Archive-663/kodakFunsaver/Canon FD/README.md

## Kodak Funsaver lens rehousing for Canon FD

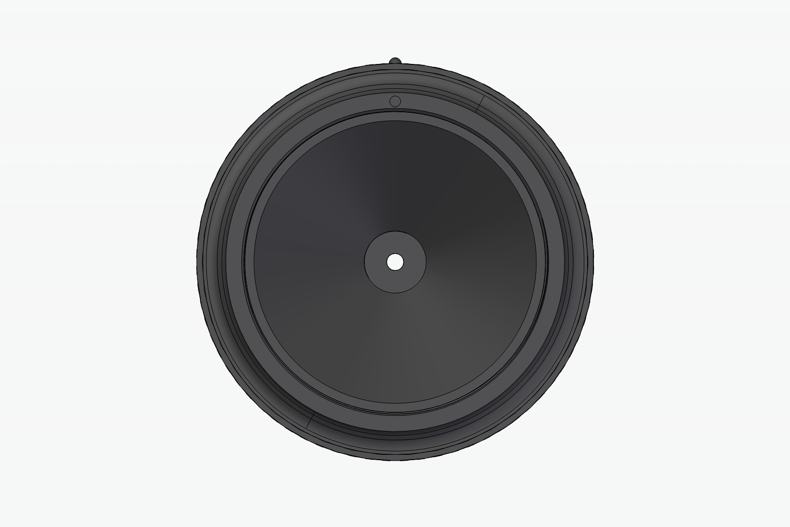
[picture p43: ASSETS/kodakFunsaver_canonFD.jpg]
KFS_canonFD_1

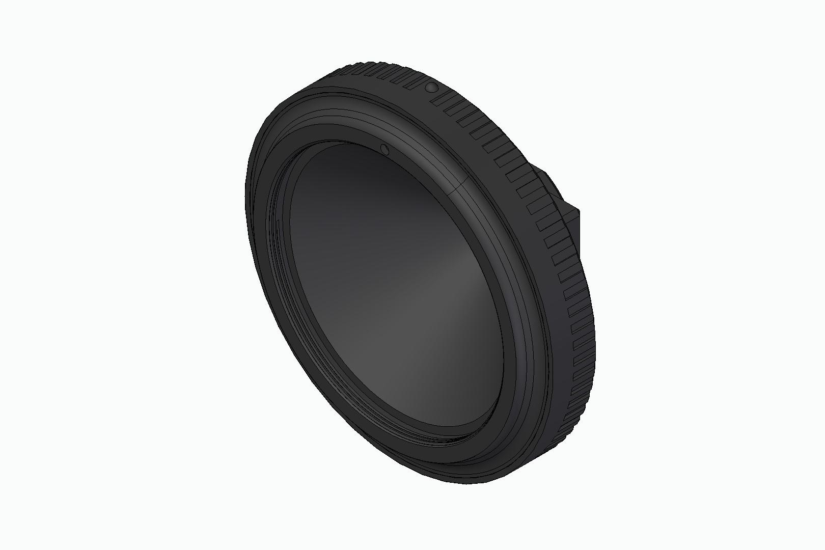
[picture p44: ASSETS/kodakFunsaver_canonFD_1.jpg]
KFS_canonFD_2

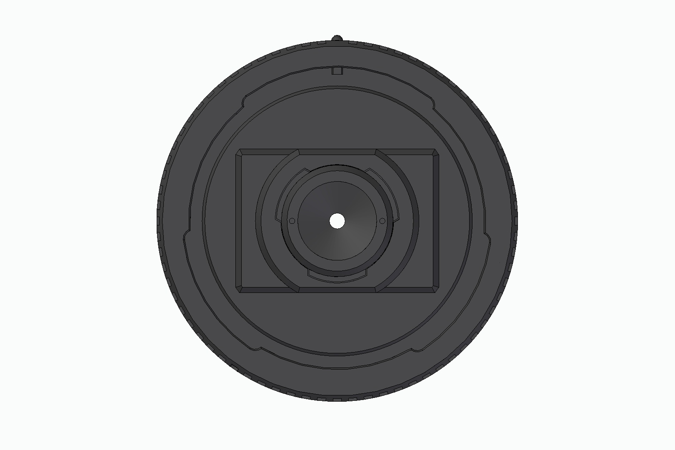
[picture p45: ASSETS/kodakFunsaver_canonFD_2.jpg]
KFS_canonFD_3


### Features:
- Breech-lock mounting ring for DSLR/SLR cameras
- Standard mounting for Mirrorless cameras
- 30mm focal length
- Fixed ~f11 aperture
- Available in: Canon EF, EF-S, FD, RF; Fuji X; Leica M; M42; Nikon F DX, F FX, Z; Sony E

### Compatibility Note:
You need a Canon body that allows for mirror lock up. Some older film cameras allowed you to hold the mirror up with hardware, but there are some that link the mirror actuation to the shutter actuation so you can't lock your mirror up. Just make sure you have mirror lock up. Tested on a Canon FTb.

### What you’ll need:
- A few of M1.6 x 5mm machine screws (PETG)
  or
- A few of M1.6 x 5mm self tapping screws (PETG or ABS)
- Lens from a Kodak FunSaver (2015 and newer)
- Viewfinder lenses from a Kodak FunSaver (2015 or newer) for
  
  [Kodak Funsaver Viewfinder Housing](https://github.com/Archive-663/kodakFunsaver/tree/main/viewFinder)
  
- [49mm Lens Cap](https://github.com/Archive-663/lensCaps)

### What would be helpful:
- M1.4 drill bit
- M1.8/M2 drill bit
- digi-Process C-41 Lightroom Preset

    [Lightroom Presets](https://github.com/Archive-663/lightroomPresets)

    This preset develops your photos for a flat base reminiscent of old Kodak negative scans. It does not remove the distortion as it is a characteristic of the lens and of the photos that are produced with film. If you want to remove the distortion; set your distortion slider to ~ -12.

### Helpful Links:
- [Kodak FunSaver Disassembly](https://www.youtube.com/watch?v=eMyq5sUIDkU)

- [Kodak FunSaver Lens Removal](https://www.youtube.com/watch?v=mniP1P2PrpM)

- [Kodak FunSaver Lens Adapter Assembly](https://www.youtube.com/watch?v=7Ed5-oDCAb8)

### Printing help:
I print with PETG because it's pretty easy to set up with and dial in. If you want to use something else, go for it. I'd stay away from PLA because it's not the best in heat and against solvents. 

Generally, all my designs have chamfers on the print face of the STL.

Please view the printOrientation.3mf file for help with orienting the parts on the printer bed. 

### Assembly help:
I suggest drilling holds to their correct tap size before tapping. The m1.6 holes should be drilled out to 1.4 then tapped with the m1.6 tap. The Rotator holes should be drilled out with an m2 or m1.8 drill bit.

When assembling the rotating assemblies use some synthetic grease similar to Super Lube PTFE or keycap lube to make the rotate function smoother. 

Please view the _assembly.stp file for help in parts orientation. If you do not have a CAD program, <a href="https://www.freecad.org/downloads.php" target="_blank">download FreeCAD</a> to view the assembly file and better understand how it should assemble.

### Help support Archive 663 with a dontation or monthly sub
