Archive-663/kodakFunsaver/ASSETS/kodakFunsaver_sample (1).jpg

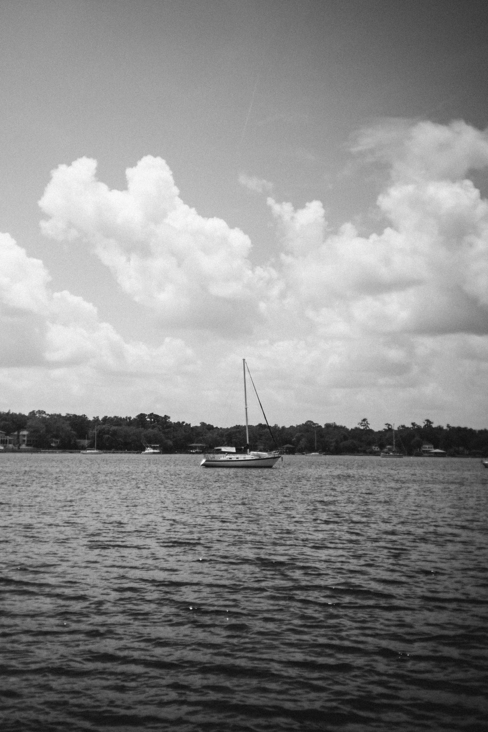
ASSETS/kodakFunsaver_sample (1).jpg
