Archive-663/kodakFunsaver/ASSETS/kodakFunsaver_sample (2).jpg

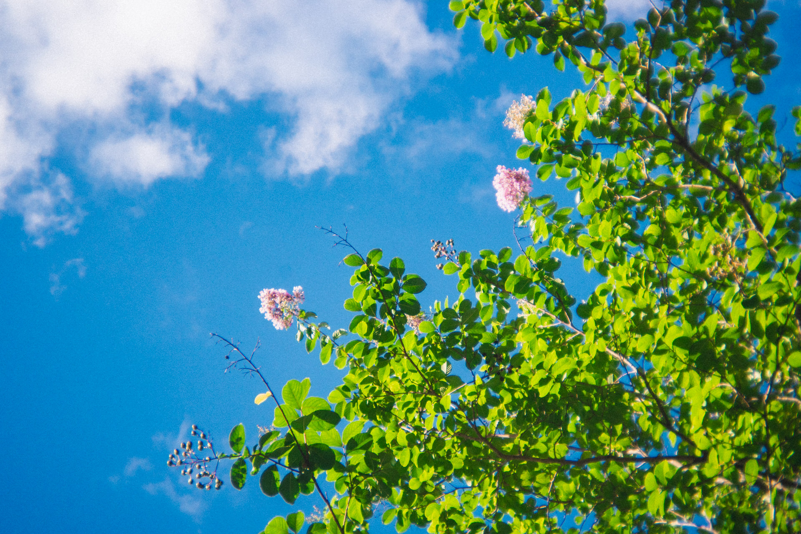
ASSETS/kodakFunsaver_sample (2).jpg
