Archive-663/kodakFunsaver/ASSETS/kodakFunsaver_sample (3).jpg

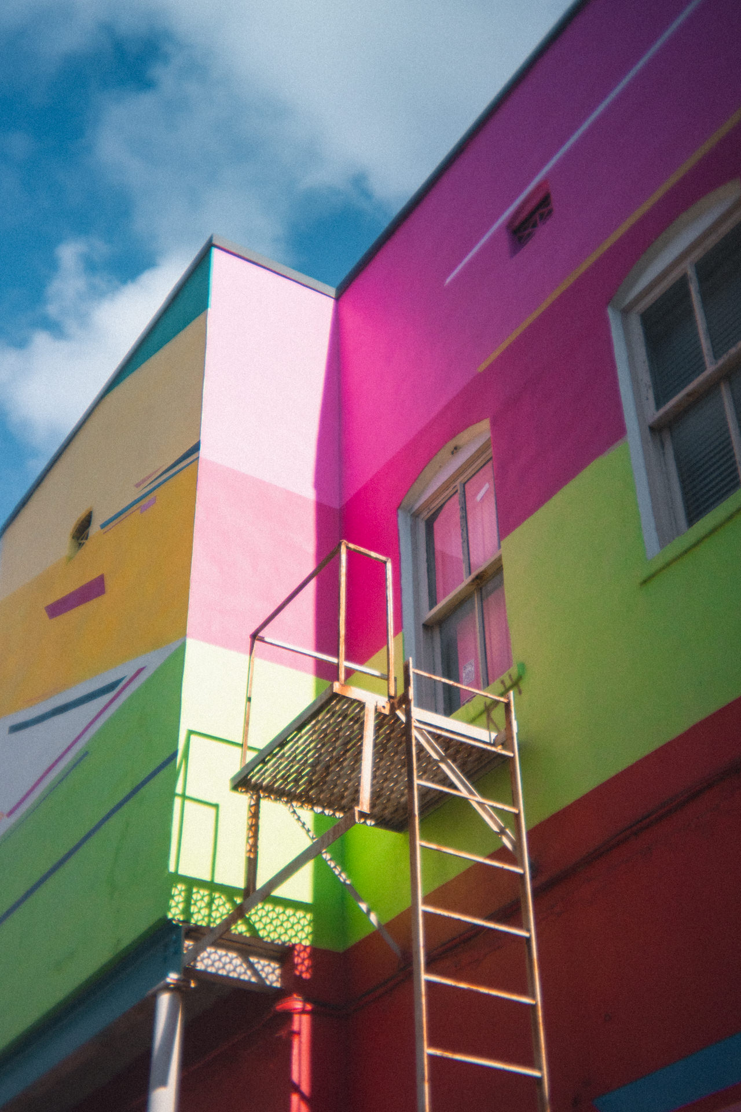
ASSETS/kodakFunsaver_sample (3).jpg
