Archive-663/kodakFunsaver/ASSETS/kodakFunsaver_sample (4).jpg

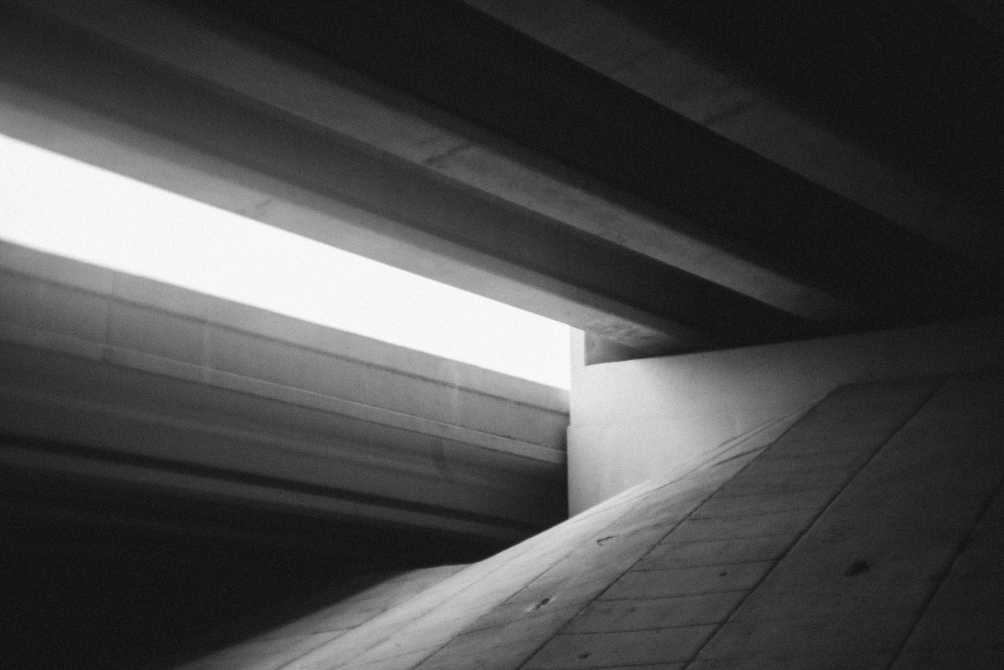
ASSETS/kodakFunsaver_sample (4).jpg
