Archive-663/kodakFunsaver/ASSETS/kodakFunsaver_sample (7).jpg

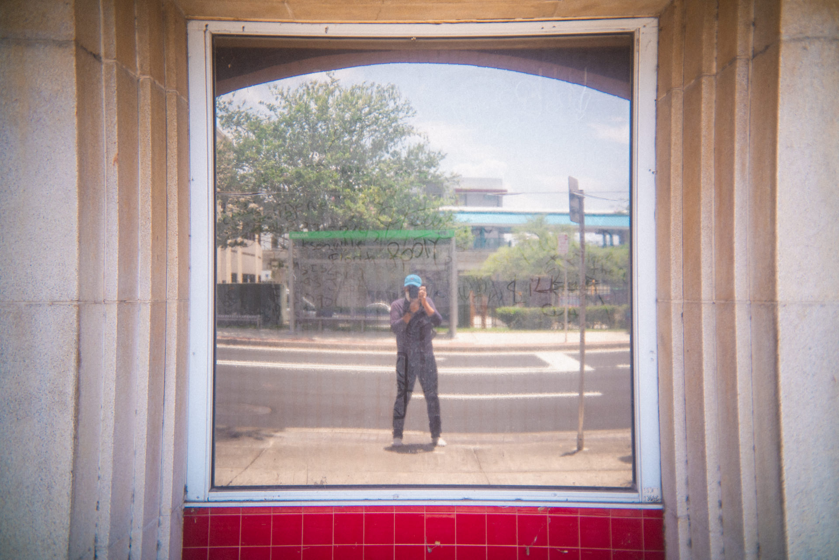
ASSETS/kodakFunsaver_sample (7).jpg
