Archive-663/kodakFunsaver/ASSETS/kodakFunsaver_sample (8).jpg

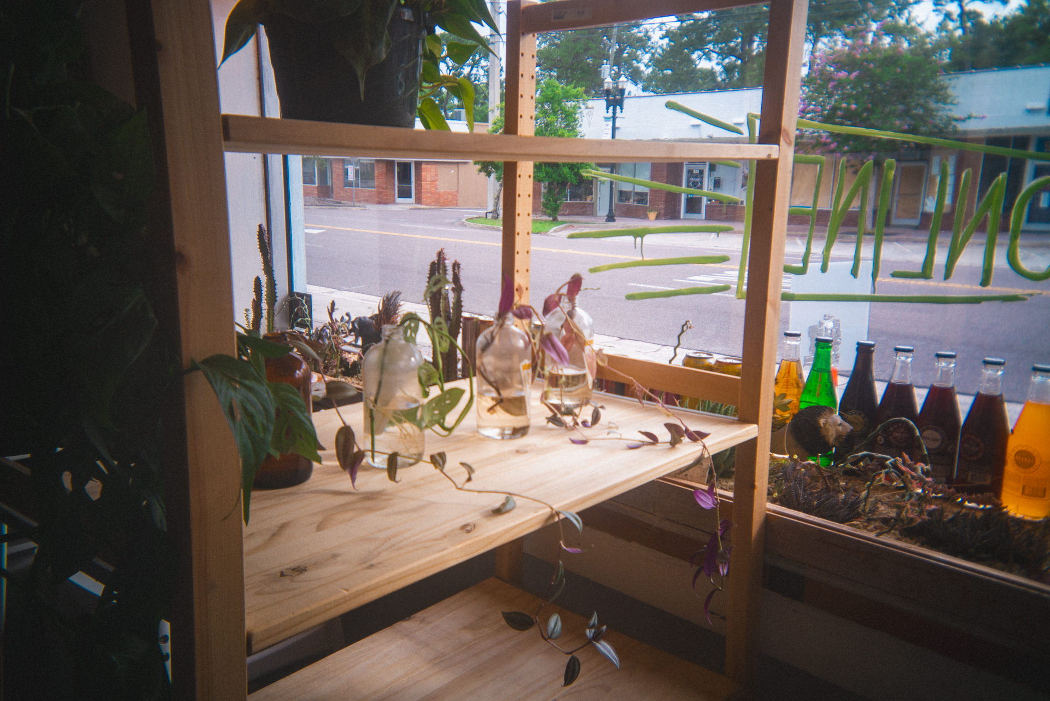
ASSETS/kodakFunsaver_sample (8).jpg
