Archive-663/kodakFunsaver/ASSETS/kodakFunsaver_sample (9).jpg

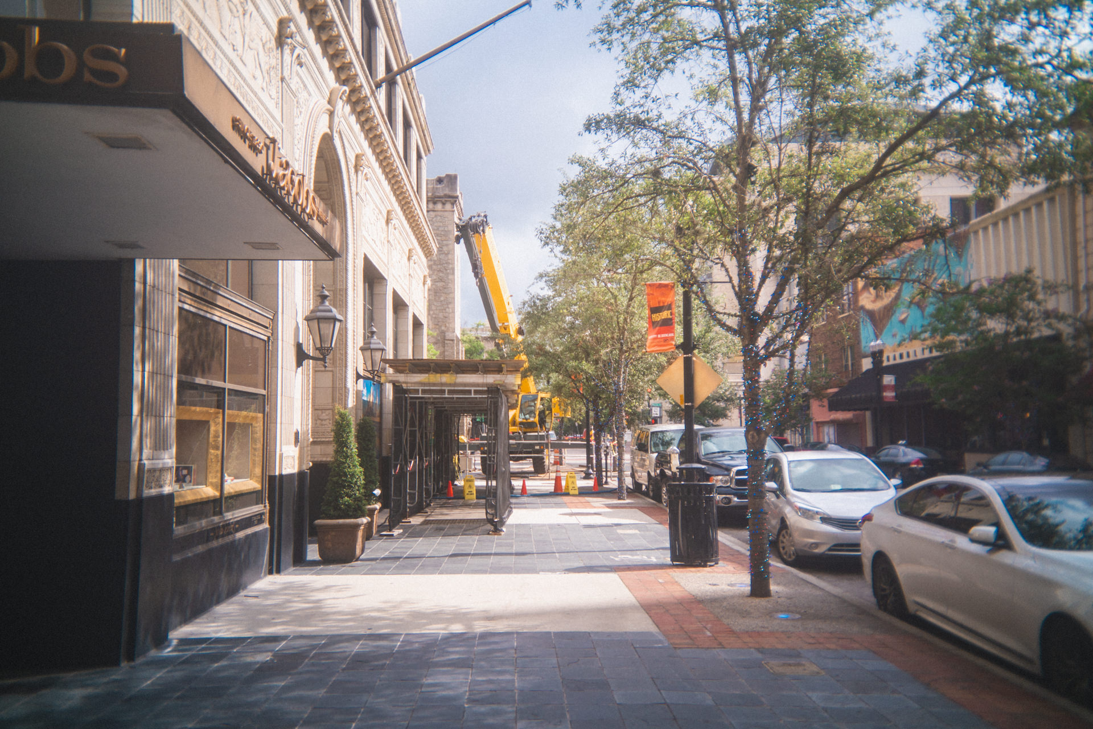
ASSETS/kodakFunsaver_sample (9).jpg
