Archive-663/kodakFunsaver/ASSETS/kodakFunsaver_sample (10).jpg

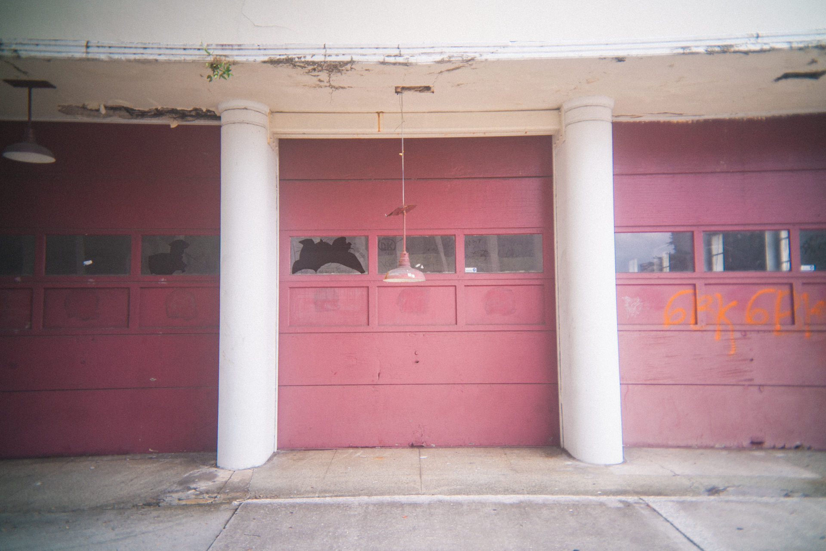
ASSETS/kodakFunsaver_sample (10).jpg
