Archive-663/kodakFunsaver/ASSETS/kodakFunsaver_sample (11).jpg

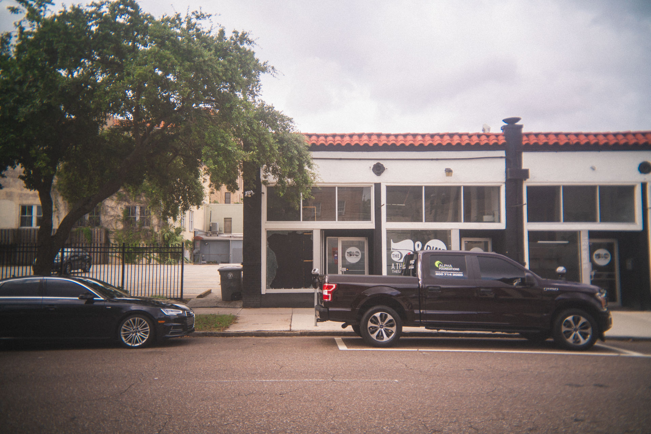
ASSETS/kodakFunsaver_sample (11).jpg
