Archive-663/kodakFunsaver/ASSETS/kodakFunsaver_sample (12).jpg

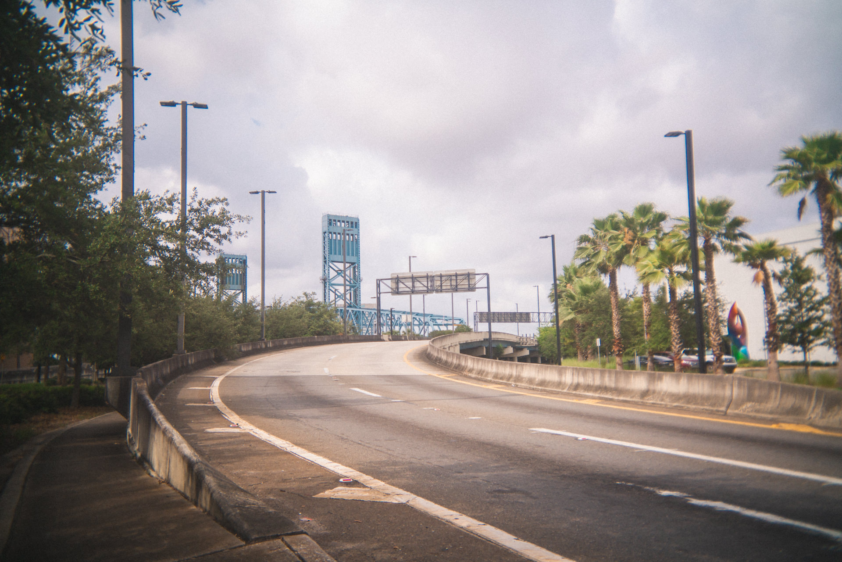
ASSETS/kodakFunsaver_sample (12).jpg
