Archive-663/kodakFunsaver/ASSETS/kodakFunsaver_sample (13).jpg

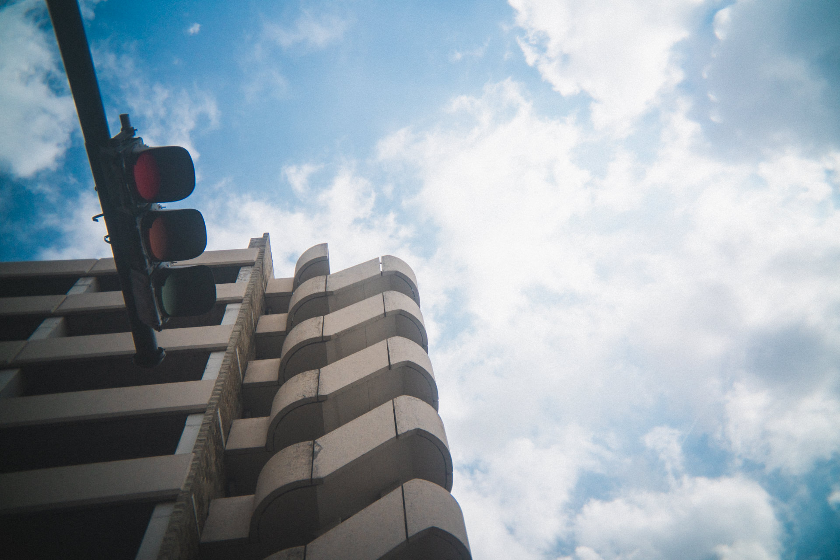
ASSETS/kodakFunsaver_sample (13).jpg
