Archive-663/kodakFunsaver/ASSETS/kodakFunsaver_sample (14).jpg

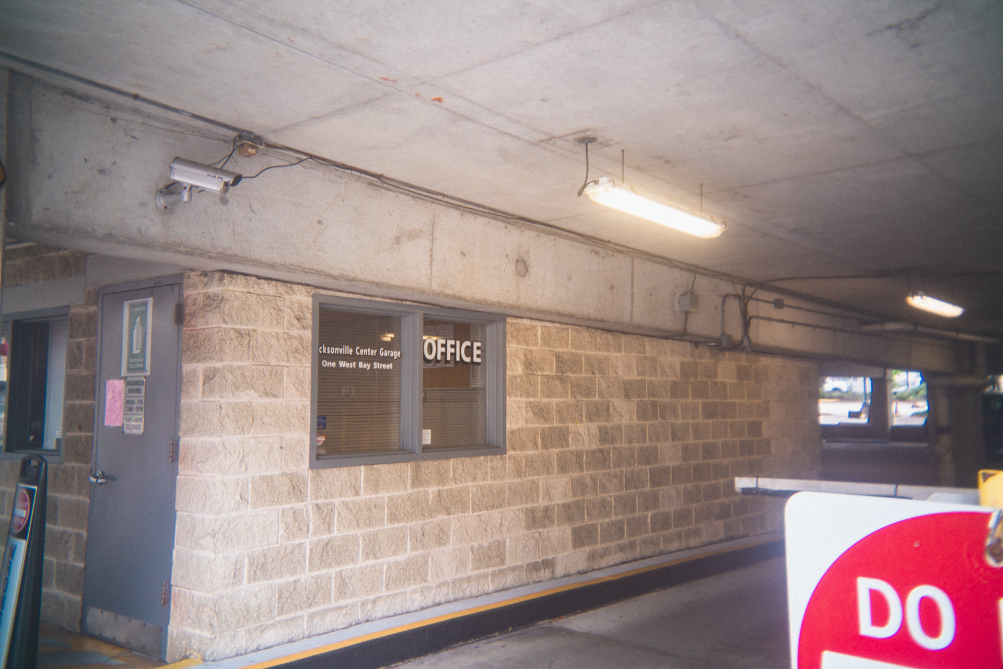
ASSETS/kodakFunsaver_sample (14).jpg
