Archive-663/kodakFunsaver/ASSETS/kodakFunsaver_sample (15).jpg

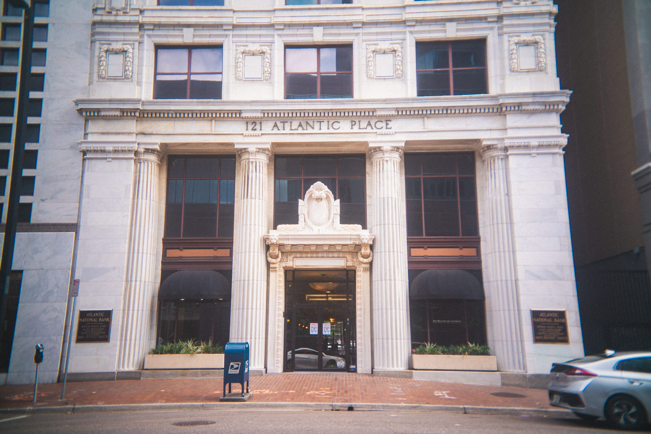
ASSETS/kodakFunsaver_sample (15).jpg
