Archive-663/kodakFunsaver/ASSETS/kodakFunsaver_sample (16).jpg

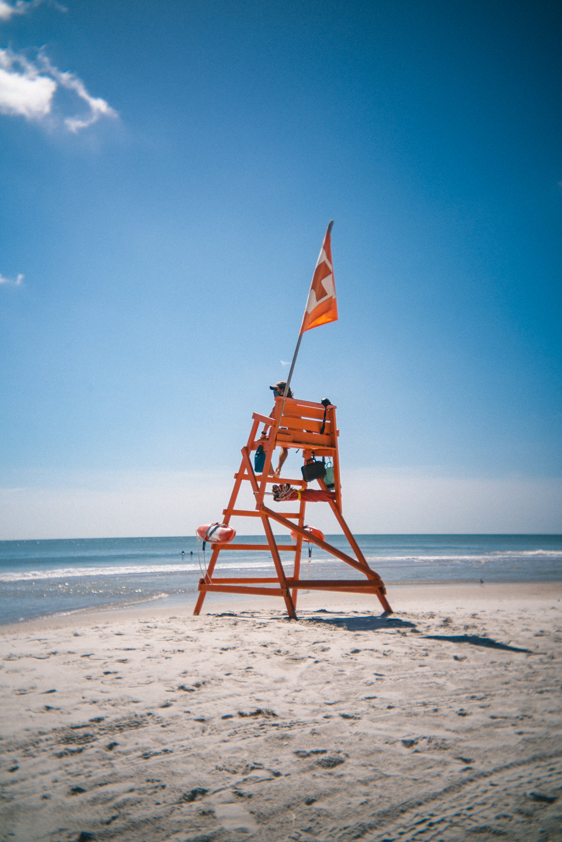
ASSETS/kodakFunsaver_sample (16).jpg
