Archive-663/kodakFunsaver/ASSETS/kodakFunsaver_sample (18).jpg

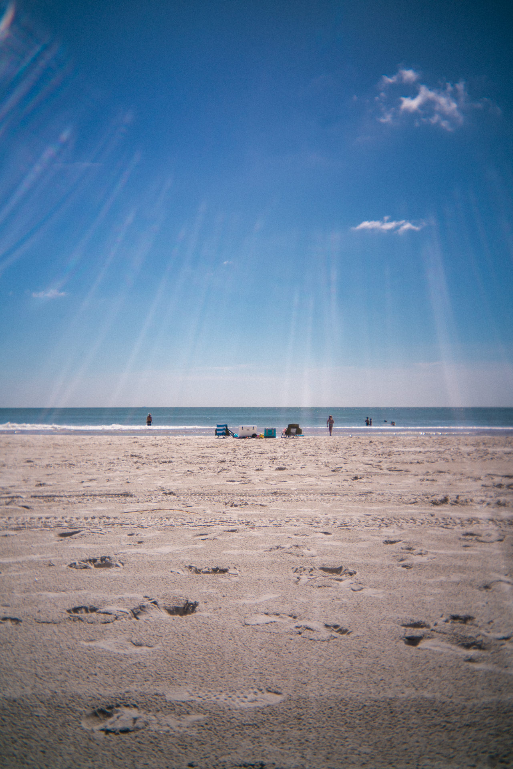
ASSETS/kodakFunsaver_sample (18).jpg
