Archive-663/kodakFunsaver/ASSETS/kodakFunsaver_sample (21).jpg

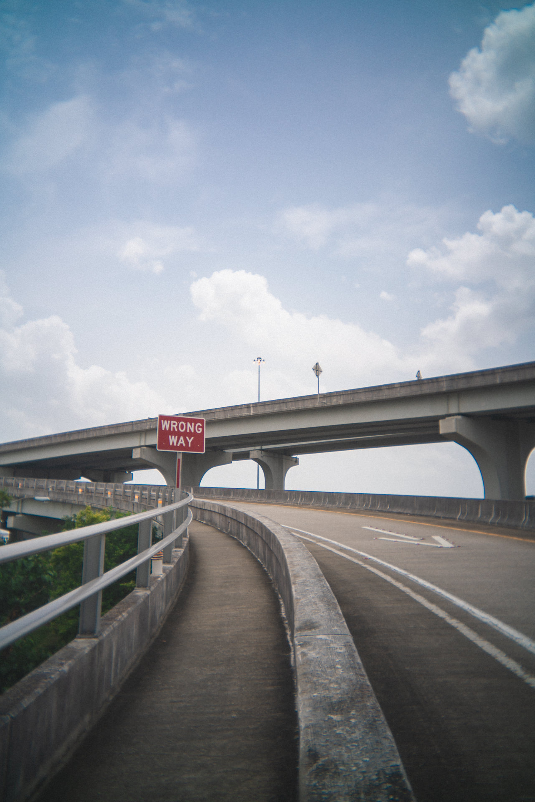
ASSETS/kodakFunsaver_sample (21).jpg
