Archive-663/kodakFunsaver/ASSETS/kodakFunsaver_sample (22).jpg

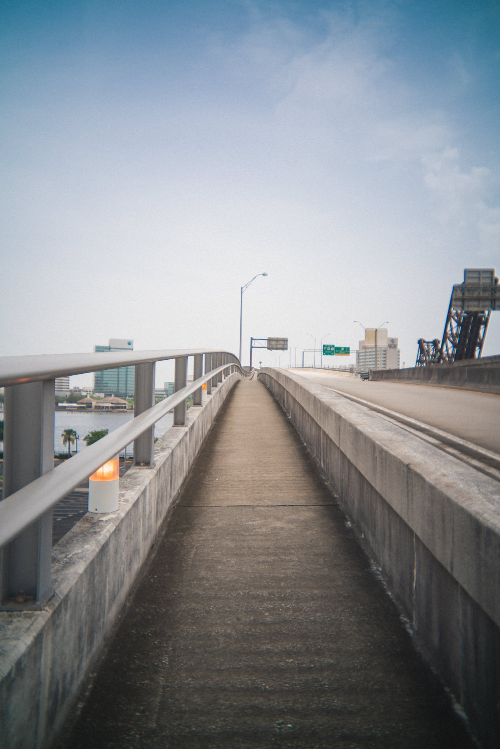
ASSETS/kodakFunsaver_sample (22).jpg
