Archive-663/kodakFunsaver/ASSETS/kodakFunsaver_sample (23).jpg

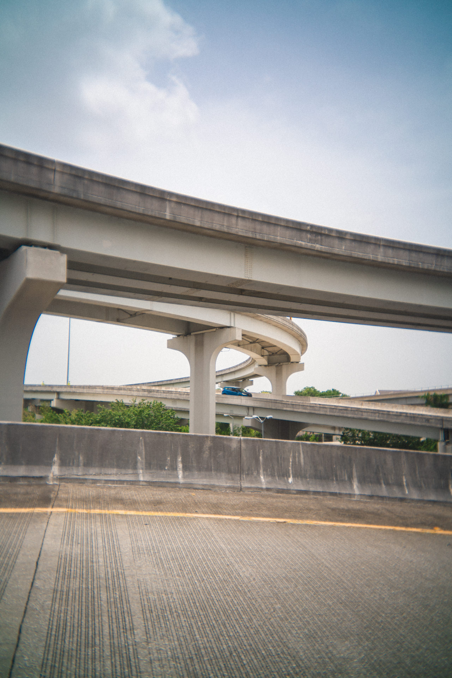
ASSETS/kodakFunsaver_sample (23).jpg
