Archive-663/kodakFunsaver/ASSETS/kodakFunsaver_sample (24).jpg

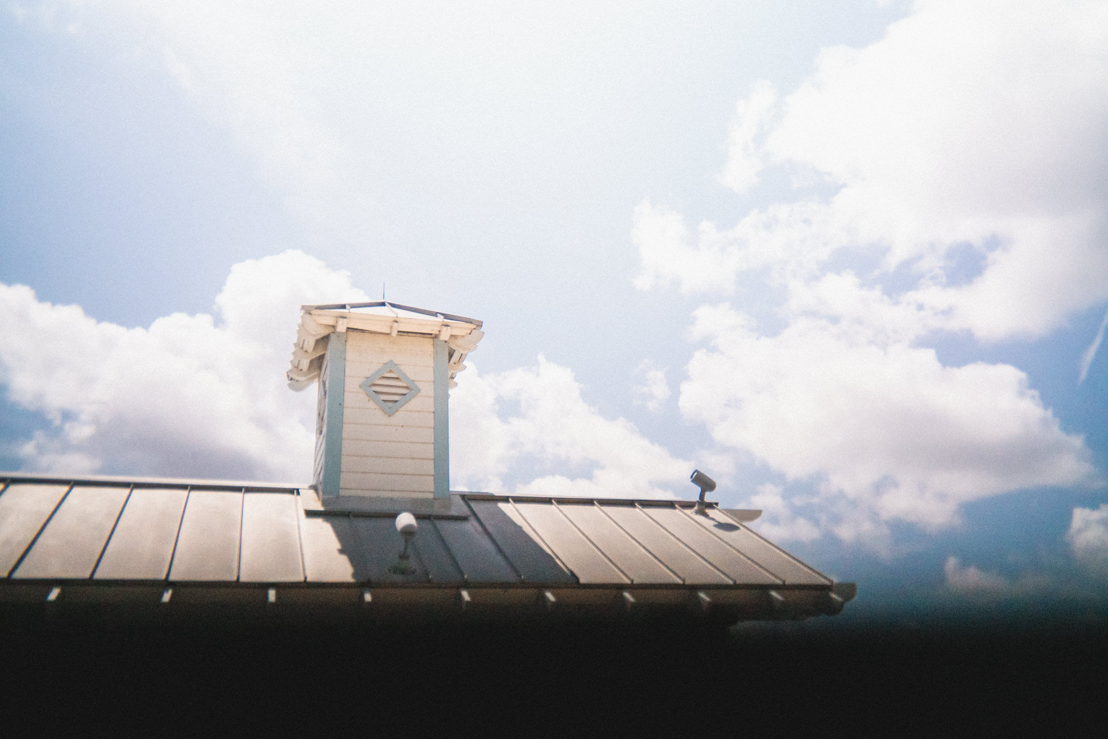
ASSETS/kodakFunsaver_sample (24).jpg
