Archive-663/kodakFunsaver/ASSETS/kodakFunsaver_sample (25).jpg

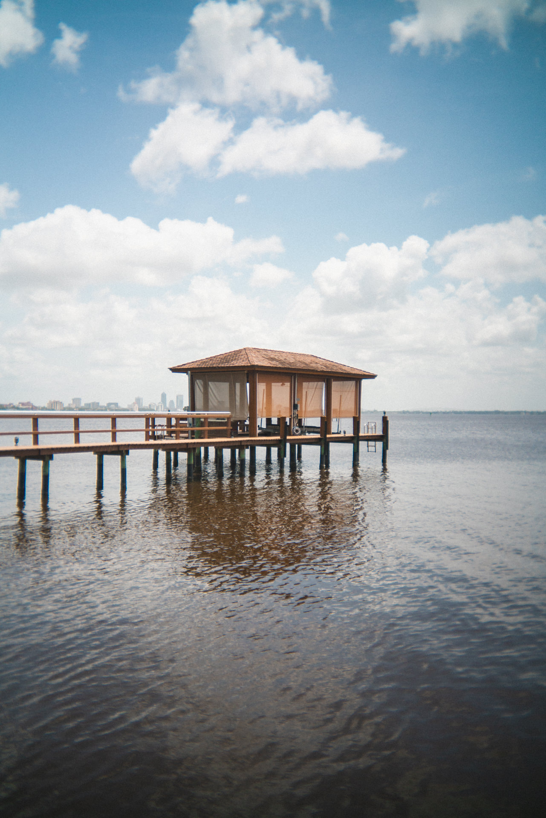
ASSETS/kodakFunsaver_sample (25).jpg
