Archive-663/kodakFunsaver/ASSETS/kodakFunsaver_sample (26).jpg

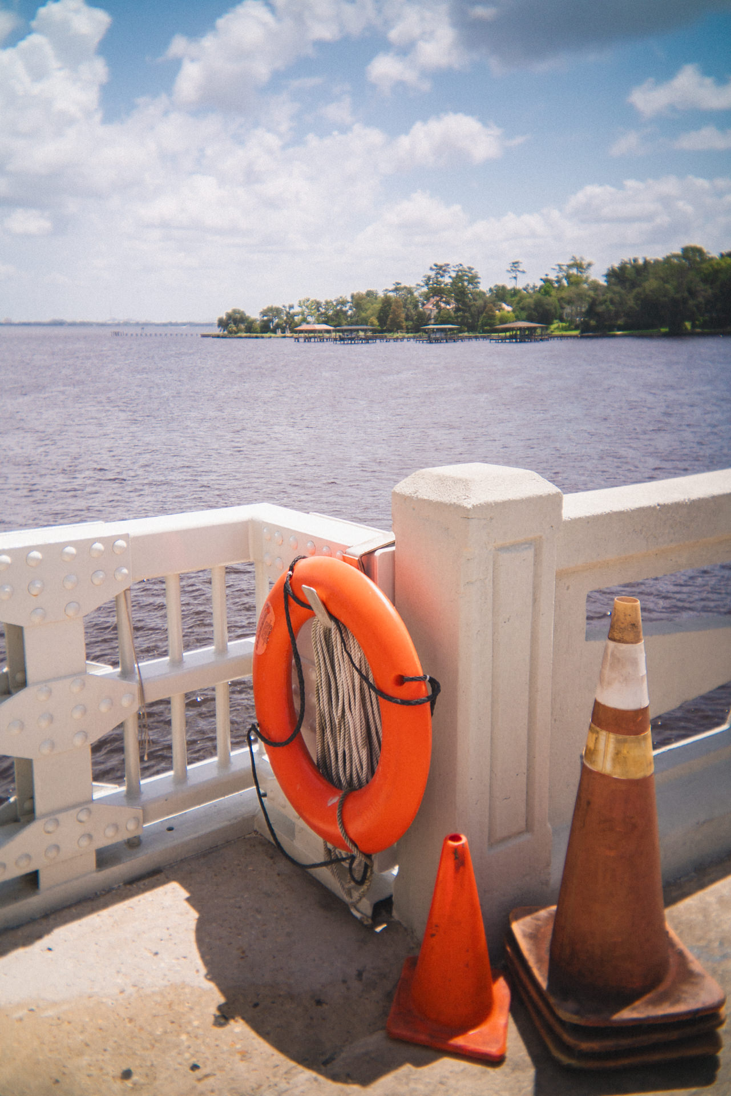
ASSETS/kodakFunsaver_sample (26).jpg
