Archive-663/kodakFunsaver/Canon EF-S/ASSETS/GMP01330.jpg

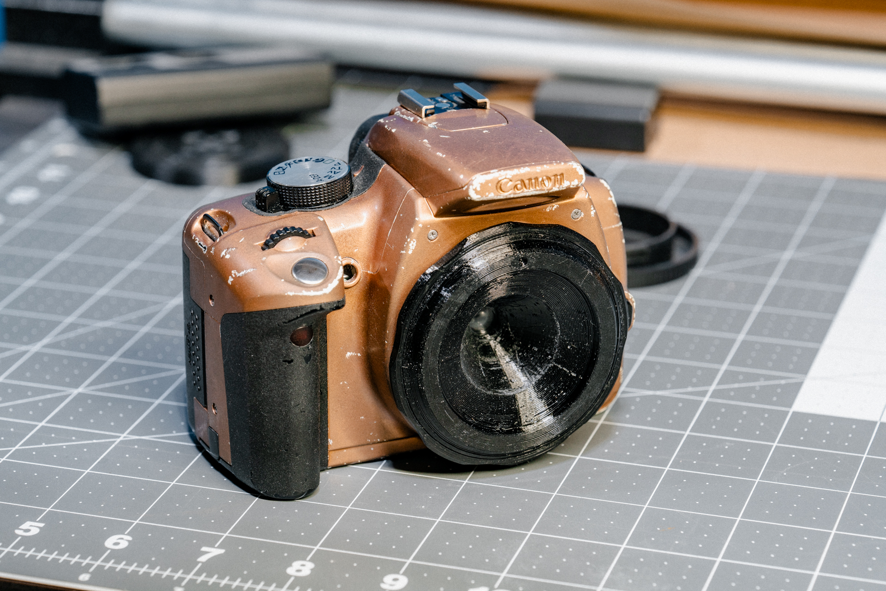
Canon EF-S/ASSETS/GMP01330.jpg
