Archive-663/kodakFunsaver/Fuji GFX/ASSETS/noEdit/NOPP_4K (12).jpg

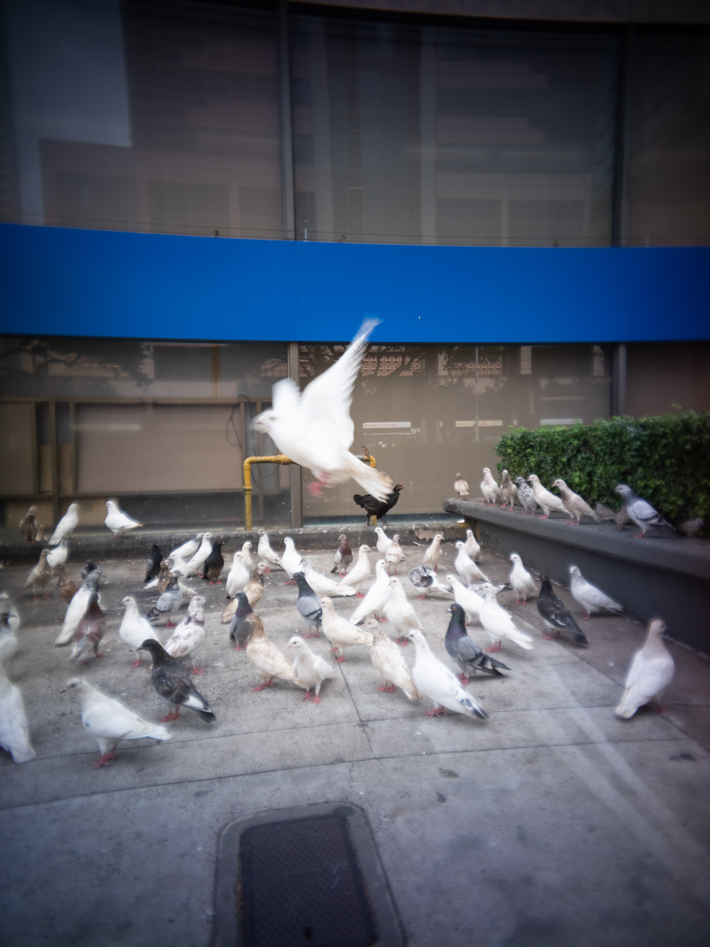
Fuji GFX/ASSETS/noEdit/NOPP_4K (12).jpg
