Archive-663/kodakFunsaver/viewFinder/viewFinder_round/STL/kodakFunsaver_viewFinder_rearSight.stl

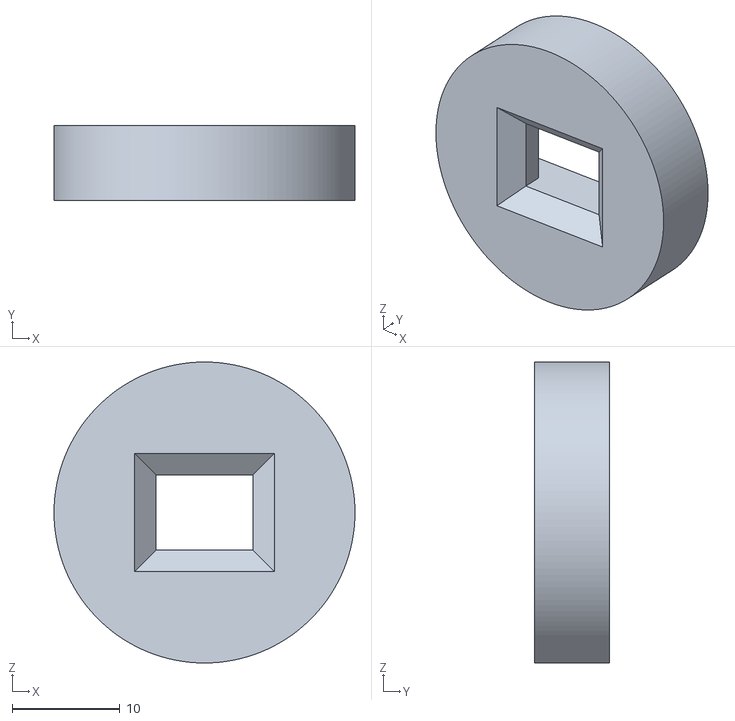
[picture p108: CAD file, 2023-06-24]
viewFinder/viewFinder_round/STL/kodakFunsaver_viewFinder_rearSight.stl
28.0 x 7.00 x 28.0
