Archive-663/kodakFunsaver/viewFinder/viewFinder_SQ/STL/kodakFunsaver_viewFinder_frontCap.stl

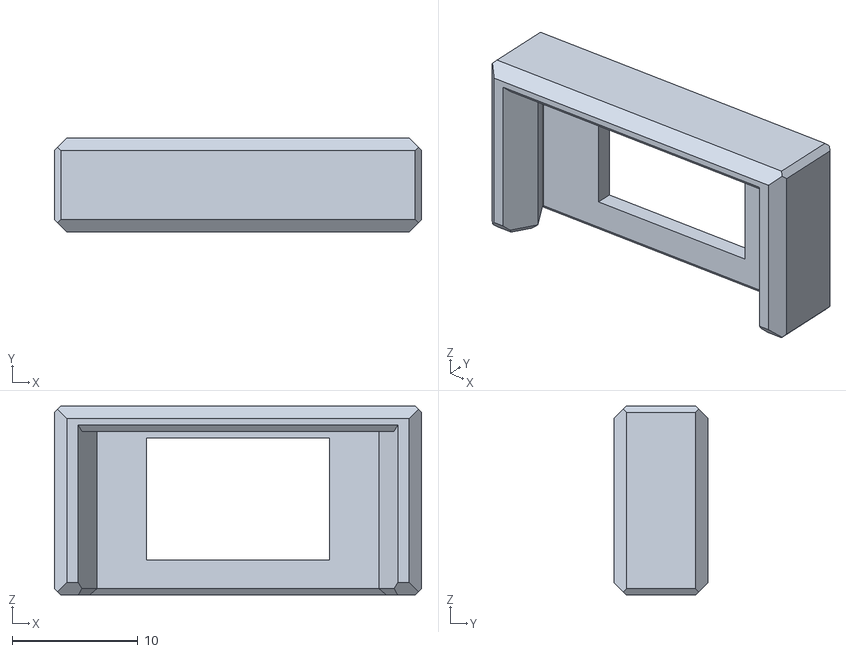
[picture p109: CAD file, 2023-11-20]
viewFinder/viewFinder_SQ/STL/kodakFunsaver_viewFinder_frontCap.stl
29.1 x 7.50 x 15.0
