Archive-663/kodakFunsaver/Canon EF-S/STL/kodakFunsaver_canonEF-S_lensLock.stl

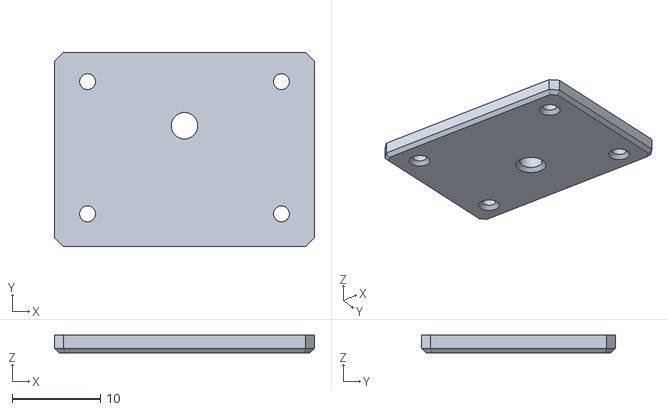
[picture p110: CAD file, 2023-11-17]
Canon EF-S/STL/kodakFunsaver_canonEF-S_lensLock.stl
29.5 x 22.0 x 2.00
