Archive-663/kodakFunsaver/Canon EF/STL/kodakFunsaver_canonEF_printOrientation.3mf

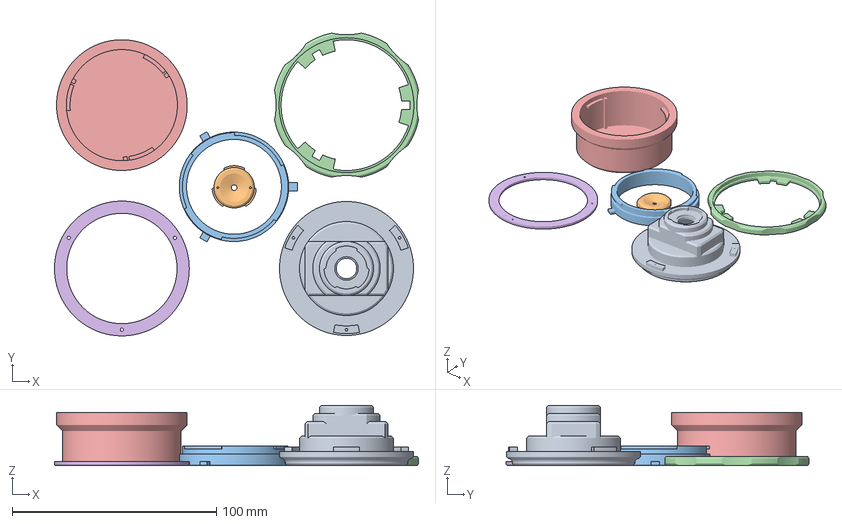
[picture p111: CAD file, 2023-11-17]
Canon EF/STL/kodakFunsaver_canonEF_printOrientation.3mf
178.3 x 148.3 x 29.5 mm
kodakFunsaver_canonEF_body.stl
kodakFunsaver_lensLock.stl
nishiKodak_canonEF_mountFlange.stl
nishiKodak_canonEF_mountLockRing.stl
baseRearCap_canonEF_KFS.stl
nishiKodak_canonEF_mountCap.stl
