Archive-663/kodakFunsaver/Canon FD/STL/nishiKodak_canonFD_breechLock.stl

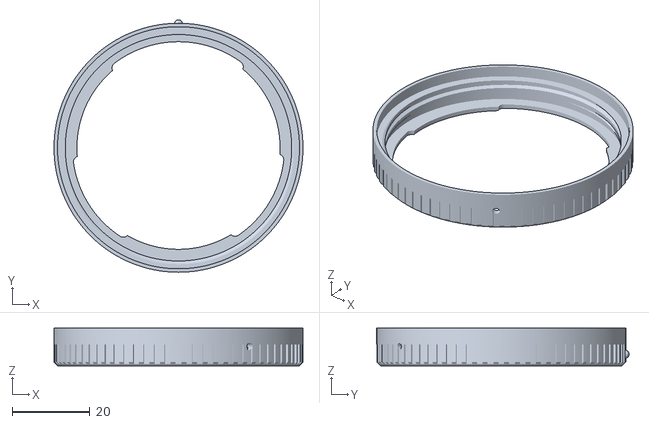
[picture p112: CAD file, 2023-11-17]
Canon FD/STL/nishiKodak_canonFD_breechLock.stl
64.0 x 64.9 x 9.75
