Archive-663/kodakFunsaver/Canon RF/STL/baseRearCap_canonRF.stl

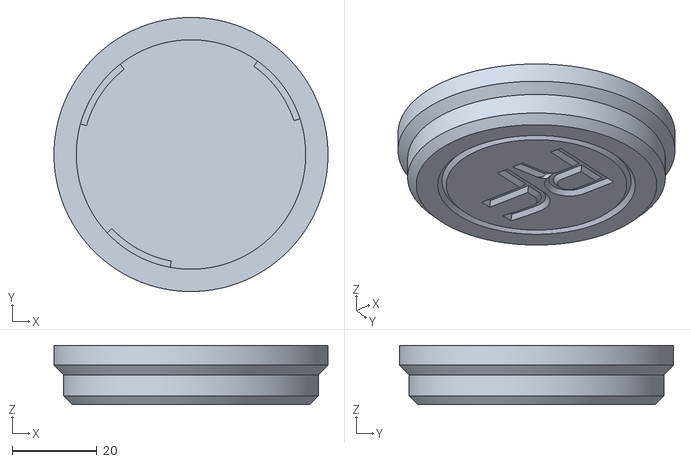
[picture p113: CAD file, 2023-11-17]
Canon RF/STL/baseRearCap_canonRF.stl
64.5 x 64.5 x 13.9
