Archive-663/kodakFunsaver/Fuji GFX/STEP/kodakFunsaver_fujiGFX_body.stp

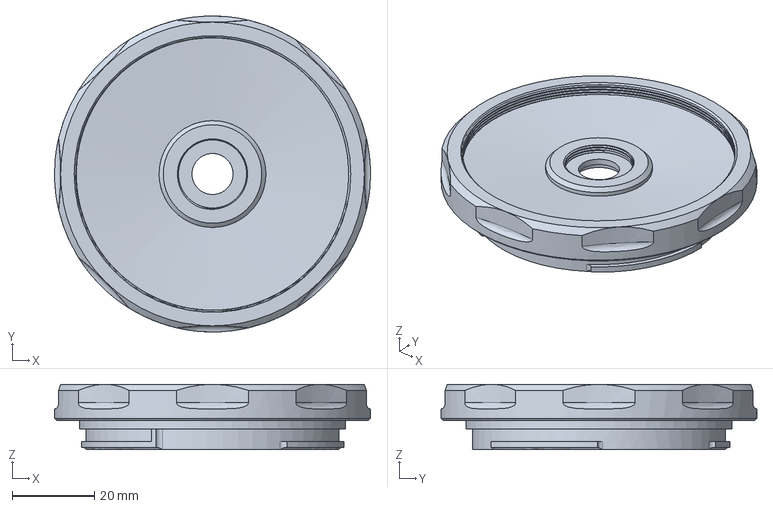
[picture p114: CAD file, 2025-04-08]
Fuji GFX/STEP/kodakFunsaver_fujiGFX_body.stp
77.0 x 77.0 x 16.0 mm
