Archive-663/kodakFunsaver/Fuji GFX/STL/kodakFunsaver_fujiGFX_printOrientation.3mf

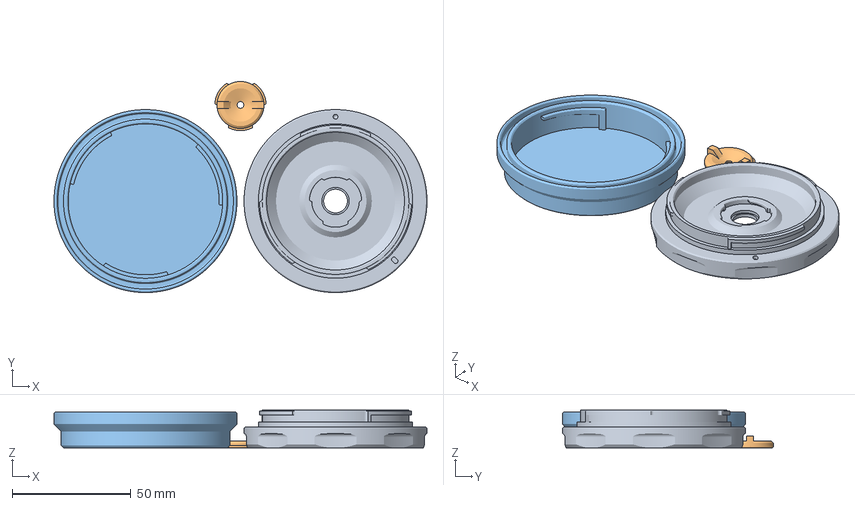
[picture p115: CAD file, 2025-04-08]
Fuji GFX/STL/kodakFunsaver_fujiGFX_printOrientation.3mf
157.0 x 88.8 x 16.0 mm
kodakFunsaver_fujiGFX_body.stl
kodakFunsaver_lensLock.stl
mountRearCapGFX.stl
