Archive-663/kodakFunsaver/Fuji X/STL/baseRearCap_fujiX.stl

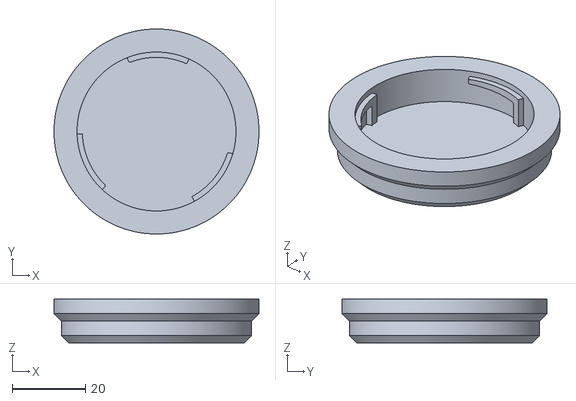
[picture p116: CAD file, 2023-11-17]
Fuji X/STL/baseRearCap_fujiX.stl
56.0 x 56.0 x 12.0
