Archive-663/kodakFunsaver/Leica M/STL/kodakFunsaver_leicaM_printOrientation.3mf

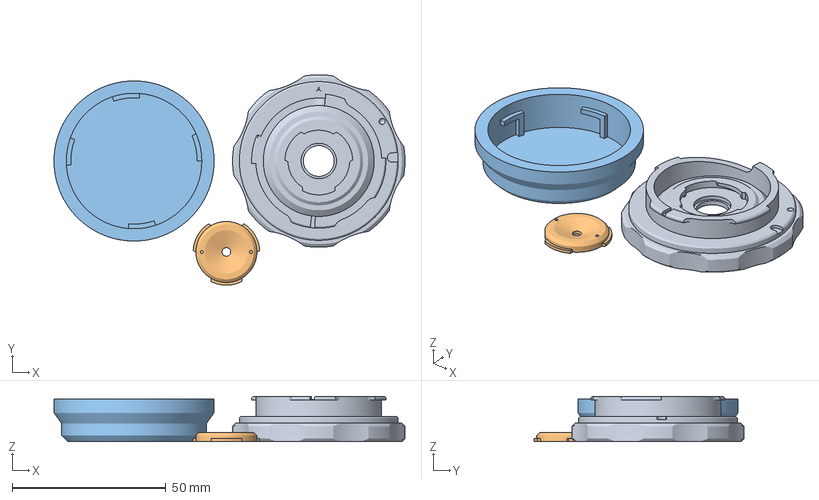
[picture p117: CAD file, 2023-11-17]
Leica M/STL/kodakFunsaver_leicaM_printOrientation.3mf
114.0 x 68.4 x 14.8 mm
kodakFunsaver_leicaM_body.stl
kodakFunsaver_lensLock.stl
baseRearCap_leicaM.stl
