Archive-663/kodakFunsaver/M42/STL/nishiKodak_M42_lensFace.stl

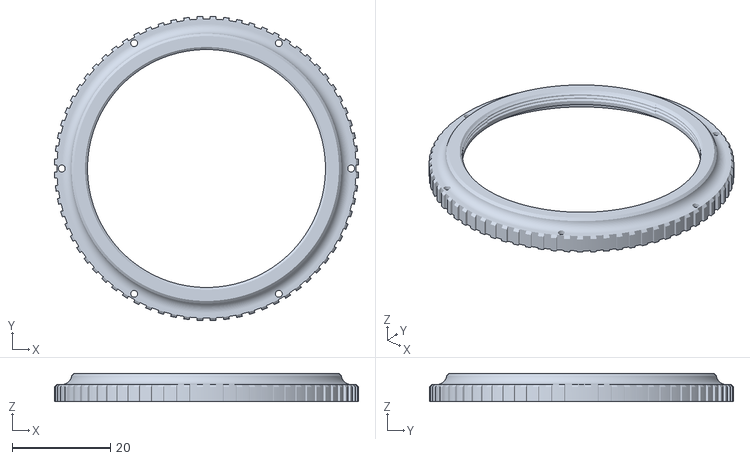
[picture p118: CAD file, 2023-11-17]
M42/STL/nishiKodak_M42_lensFace.stl
62.0 x 62.0 x 5.75
