Archive-663/kodakFunsaver/MFT/STL/kodakFunsaver_MFT_printOrientation.3mf

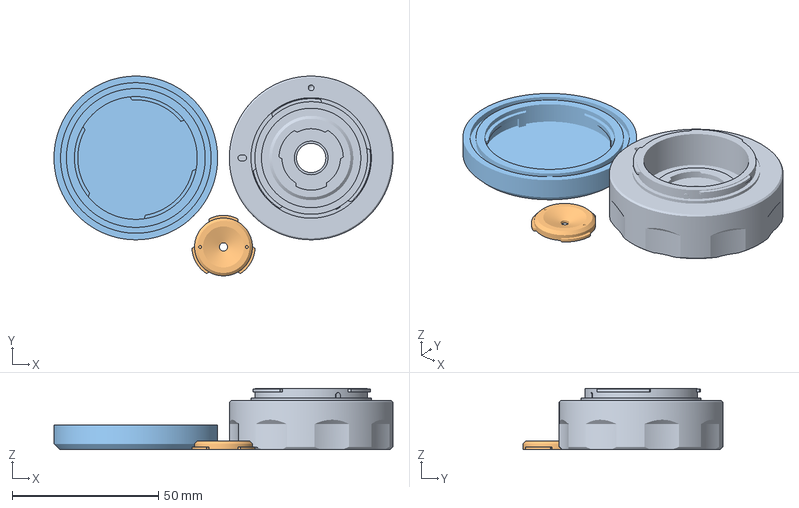
[picture p119: CAD file, 2023-11-17]
MFT/STL/kodakFunsaver_MFT_printOrientation.3mf
116.0 x 68.4 x 21.0 mm
kodakFunsaver_MFT_body.stl
kodakFunsaver_lensLock.stl
baseRearCap_MFT.stl
