Archive-663/kodakFunsaver/Nikon F DX/STL/kodakFunsaver_nikonF_DX_body.stl

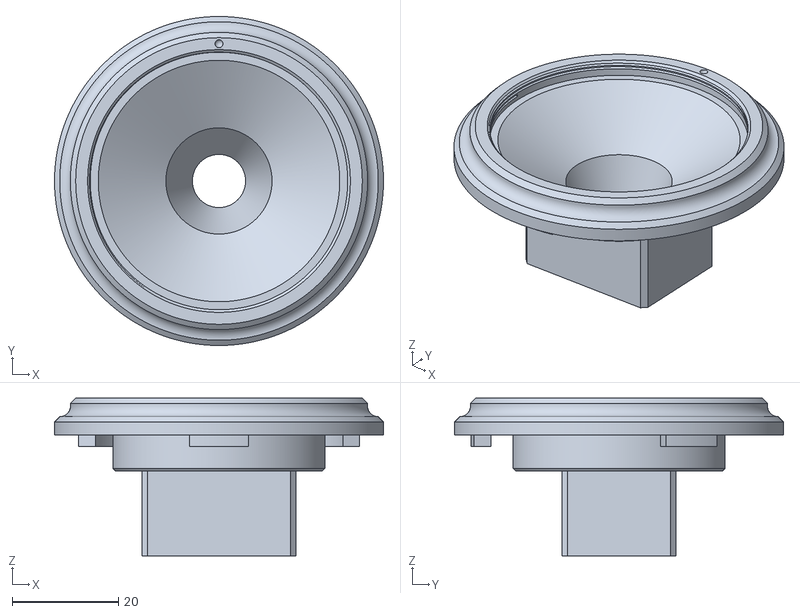
[picture p120: CAD file, 2023-11-17]
Nikon F DX/STL/kodakFunsaver_nikonF_DX_body.stl
62.0 x 62.0 x 29.8
