Archive-663/kodakFunsaver/Nikon Z/STL/kodakFunsaver_nikonZ_printOrientation.3mf

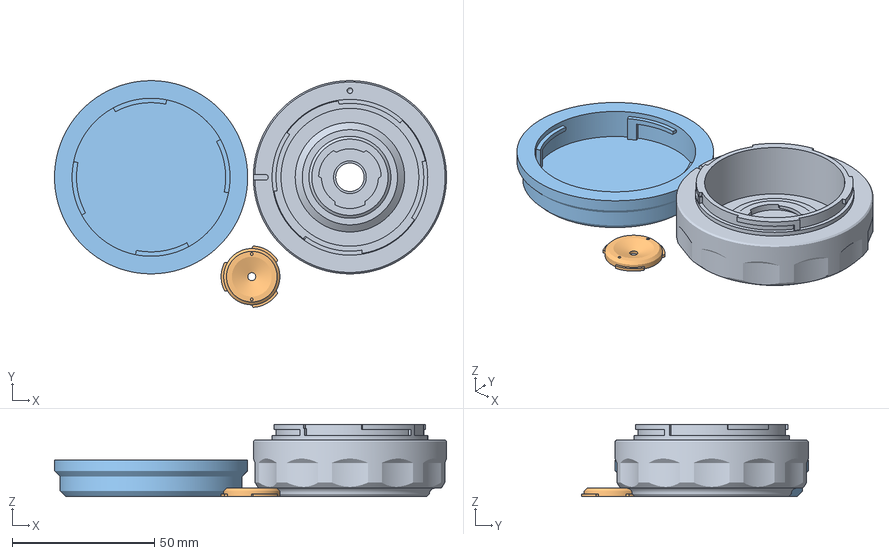
[picture p121: CAD file, 2023-11-17]
Nikon Z/STL/kodakFunsaver_nikonZ_printOrientation.3mf
138.0 x 79.8 x 25.5 mm
kodakFunsaver_nikonZ_body.stl
kodakFunsaver_lensLock.stl
baseRearCap_nikonZ.stl
