Archive-663/kodakFunsaver/Sony E/STL/baseRearCap_sonyE.stl

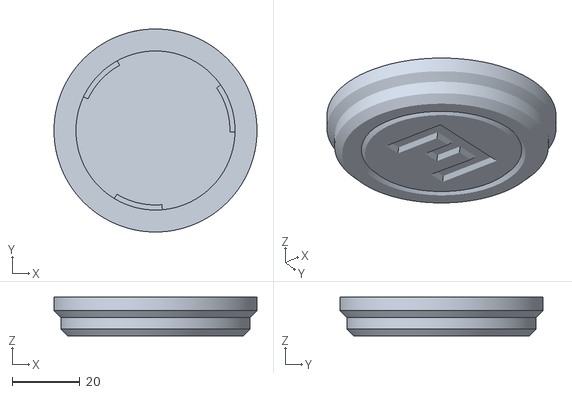
[picture p122: CAD file, 2023-11-17]
Sony E/STL/baseRearCap_sonyE.stl
60.0 x 60.0 x 11.5
