Archive-663/kodakFunsaver/viewFinder/viewFinder_round/STL/kodakFunsaver_viewFinder_frontCap.stl

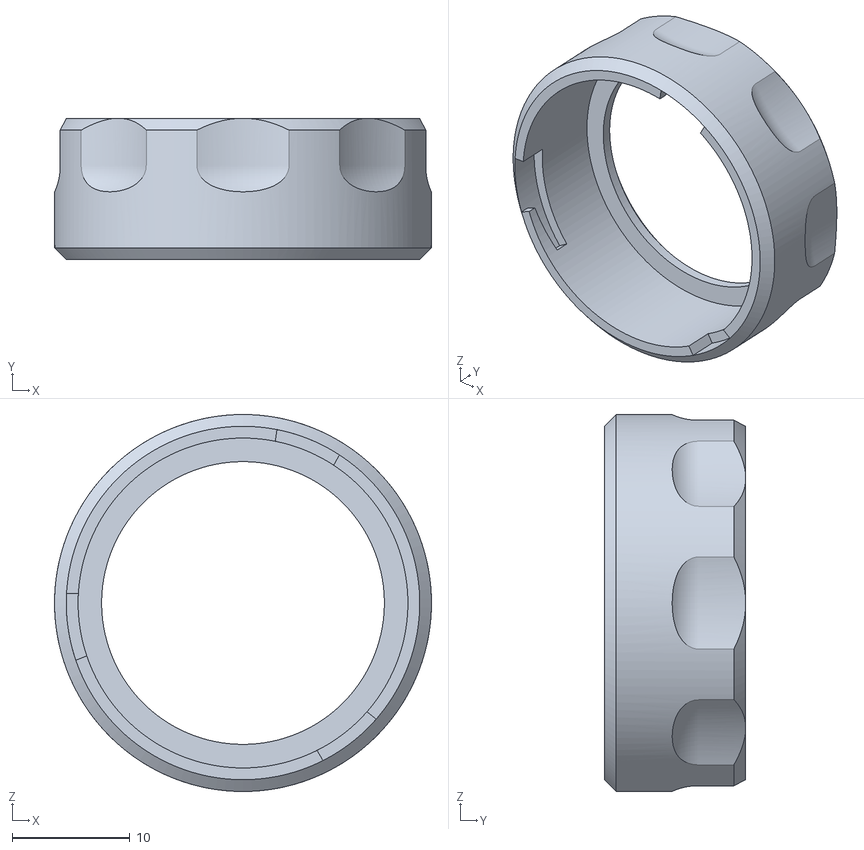
[picture p123: CAD file, 2023-06-24]
viewFinder/viewFinder_round/STL/kodakFunsaver_viewFinder_frontCap.stl
32.0 x 12.0 x 32.0
