Archive-663/kodakFunsaver/viewFinder/viewFinder_SQ/STL/kodakFunsaver_viewFinder_rearCap.stl

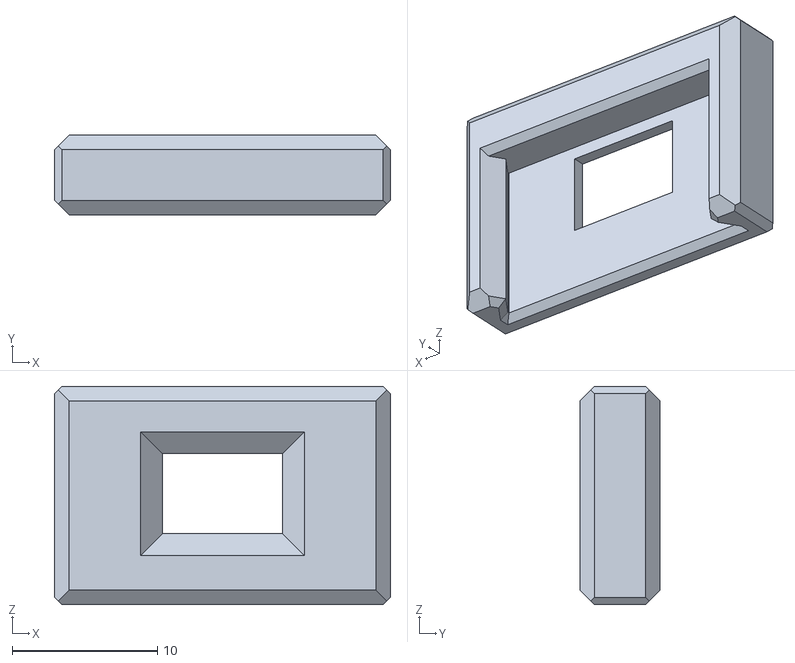
[picture p124: CAD file, 2023-11-20]
viewFinder/viewFinder_SQ/STL/kodakFunsaver_viewFinder_rearCap.stl
23.1 x 5.50 x 15.0
