Archive-663/kodakFunsaver/Canon EF-S/STL/nishiKodak_canonEF_mountFlange.stl

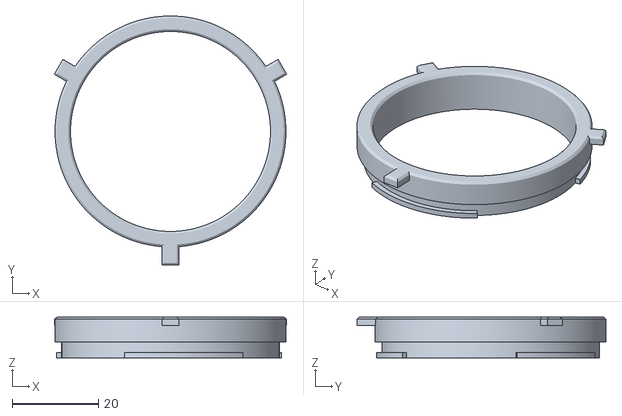
[picture p125: CAD file, 2023-11-17]
Canon EF-S/STL/nishiKodak_canonEF_mountFlange.stl
54.0 x 57.8 x 9.50
