Archive-663/kodakFunsaver/Canon EF/STL/nishiKodak_canonEF_mountLockRing.stl

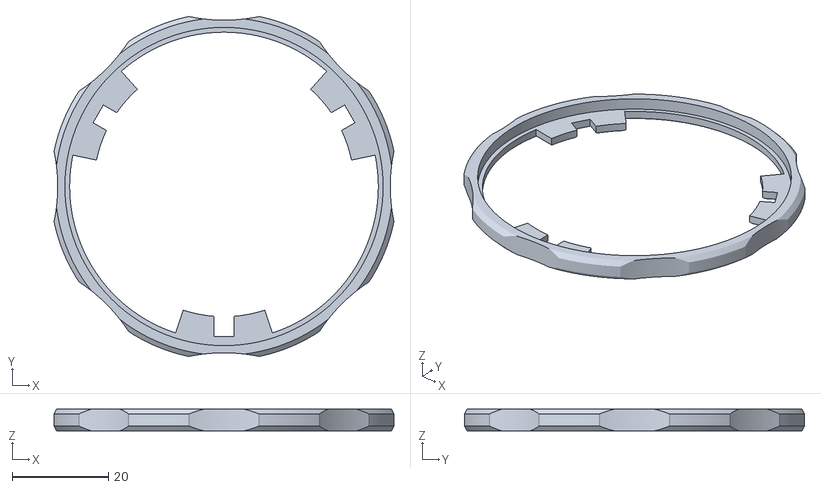
[picture p126: CAD file, 2023-11-17]
Canon EF/STL/nishiKodak_canonEF_mountLockRing.stl
70.5 x 70.5 x 4.50
