Archive-663/kodakFunsaver/Canon FD/STL/kodakFunsaver_canonFD_printOrientation.3mf

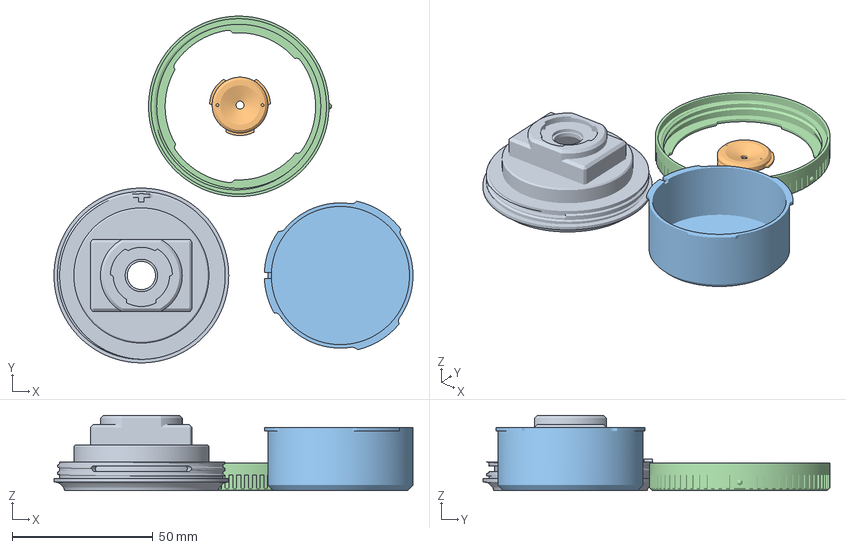
[picture p127: CAD file, 2023-11-17]
Canon FD/STL/kodakFunsaver_canonFD_printOrientation.3mf
127.4 x 123.0 x 26.8 mm
kodakFunsaver_canonFD_body.stl
kodakFunsaver_lensLock.stl
baseRearCap_canonFD_KFS.stl
nishiKodak_canonFD_breechLock.stl
