Archive-663/kodakFunsaver/Canon RF/STL/kodakFunsaver_canonRF_printOrientation.3mf

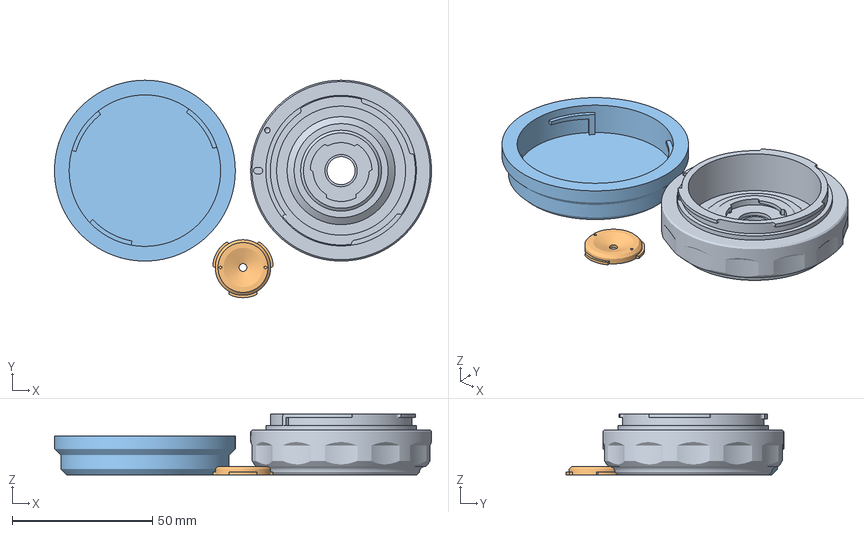
[picture p128: CAD file, 2023-11-17]
Canon RF/STL/kodakFunsaver_canonRF_printOrientation.3mf
134.5 x 77.6 x 21.7 mm
kodakFunsaver_canonRF_body.stl
kodakFunsaver_lensLock.stl
baseRearCap_canonRF.stl
