Archive-663/kodakFunsaver/Fuji X/STL/kodakFunsaver_fujiX_printOrientation.3mf

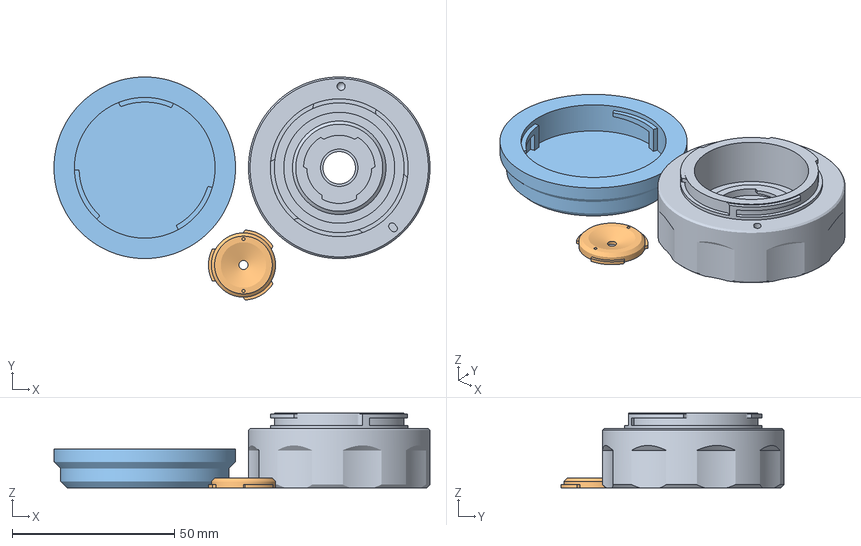
[picture p129: CAD file, 2023-11-17]
Fuji X/STL/kodakFunsaver_fujiX_printOrientation.3mf
116.0 x 68.8 x 23.1 mm
kodakFunsaver_fujiX_body.stl
kodakFunsaver_lensLock.stl
baseRearCap_fujiX.stl
