Archive-663/kodakFunsaver/Leica M/STL/baseRearCap_leicaM.stl

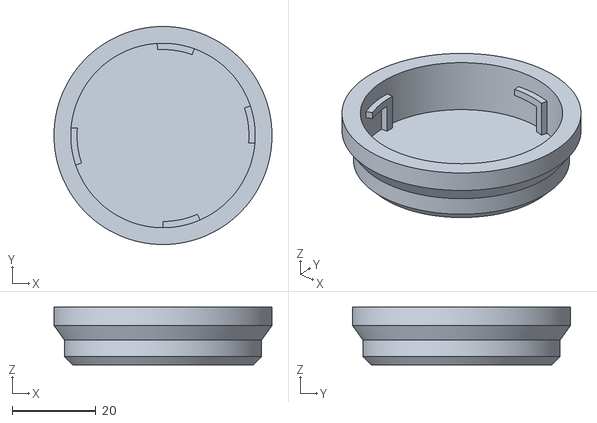
[picture p130: CAD file, 2023-11-17]
Leica M/STL/baseRearCap_leicaM.stl
52.0 x 52.0 x 13.8
