Archive-663/kodakFunsaver/M42/STL/kodakFunsaver_M42_printOrientation.3mf

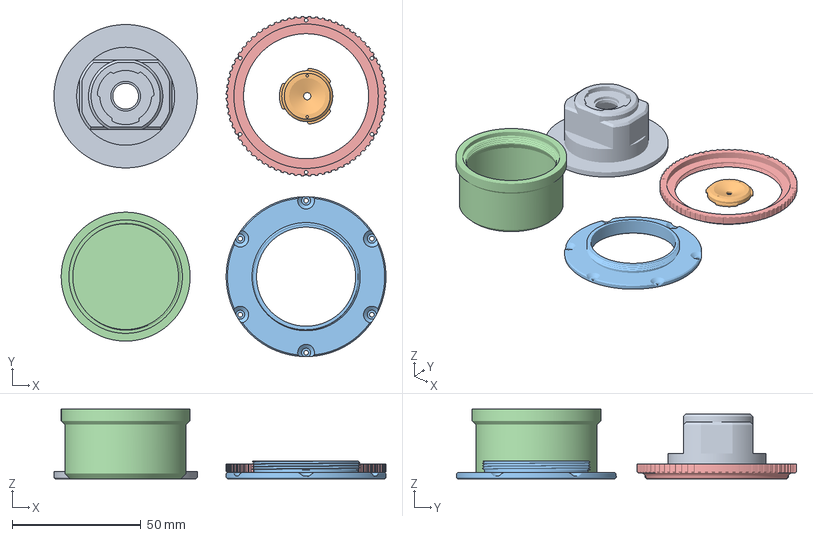
[picture p131: CAD file, 2023-11-17]
M42/STL/kodakFunsaver_M42_printOrientation.3mf
128.8 x 132.0 x 27.0 mm
kodakFunsaver_M42_body.stl
kodakFunsaver_lensLock.stl
nishiKodak_M42_mountThreads.stl
baseRearCap_M42_KFS.stl
nishiKodak_M42_lensFace.stl
