Archive-663/kodakFunsaver/MFT/STL/baseRearCap_MFT.stl

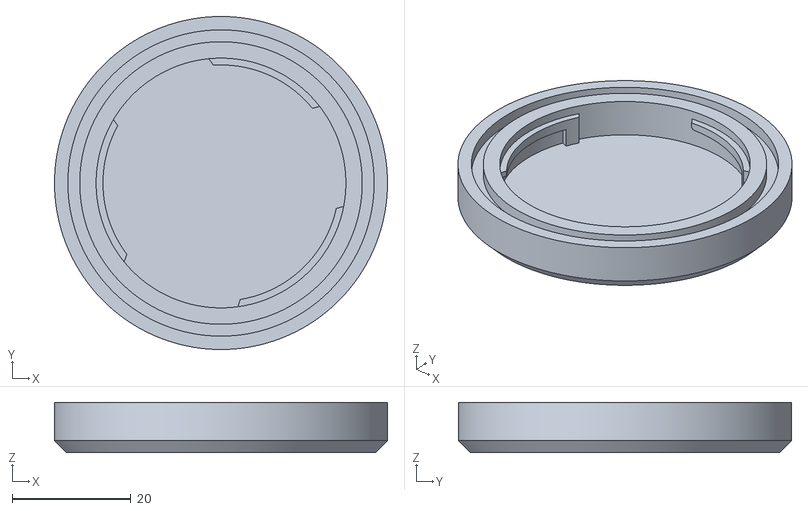
[picture p132: CAD file, 2023-11-17]
MFT/STL/baseRearCap_MFT.stl
56.0 x 56.0 x 8.45
