Archive-663/kodakFunsaver/Nikon F DX/STL/kodakFunsaver_nikonF_DX_lensLock.stl

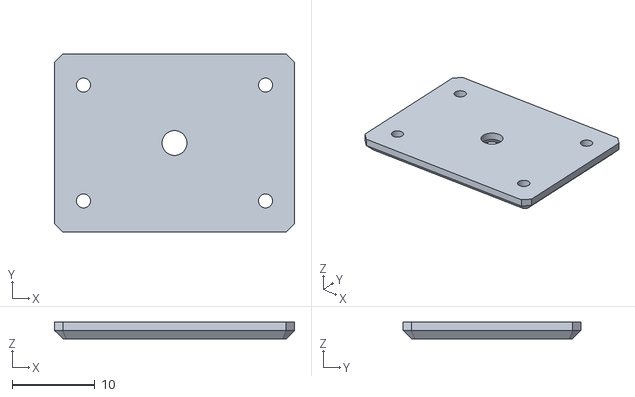
[picture p133: CAD file, 2023-11-17]
Nikon F DX/STL/kodakFunsaver_nikonF_DX_lensLock.stl
29.0 x 21.5 x 2.00
