Archive-663/kodakFunsaver/Nikon F FX/STL/kodakFunsaver_nikonF_FX_body.stl

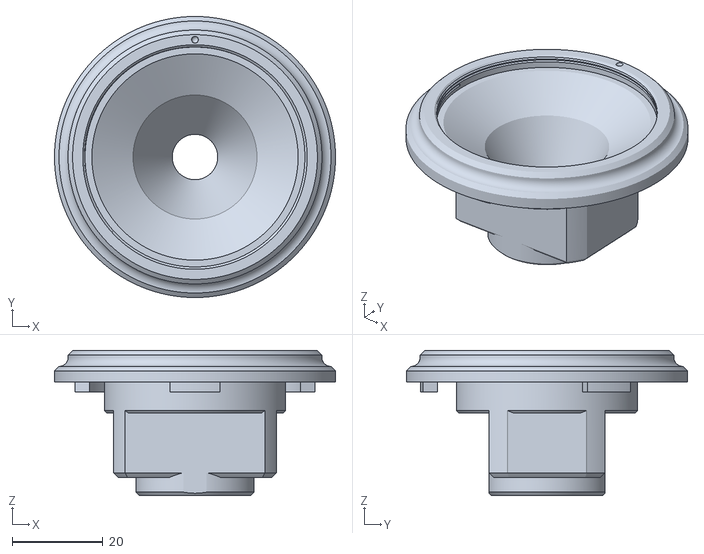
[picture p134: CAD file, 2023-11-17]
Nikon F FX/STL/kodakFunsaver_nikonF_FX_body.stl
62.0 x 62.0 x 32.0
