Archive-663/kodakFunsaver/Nikon Z/STL/baseRearCap_nikonZ.stl

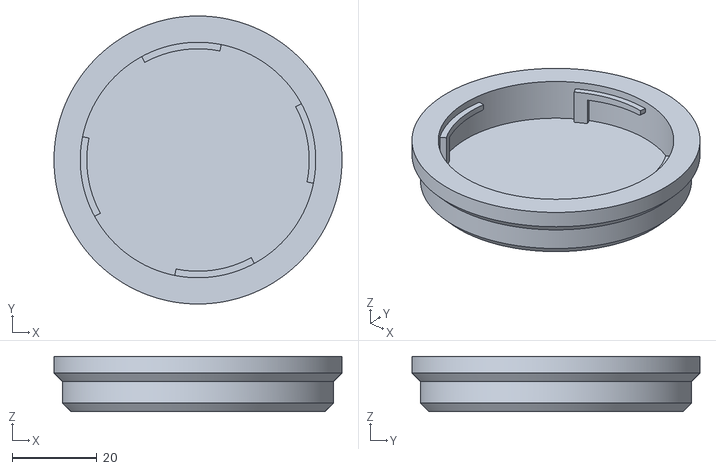
[picture p135: CAD file, 2023-11-17]
Nikon Z/STL/baseRearCap_nikonZ.stl
68.0 x 68.0 x 13.0
