Archive-663/kodakFunsaver/Sony E/STL/kodakFunsaver_sonyE_printOrientation.3mf

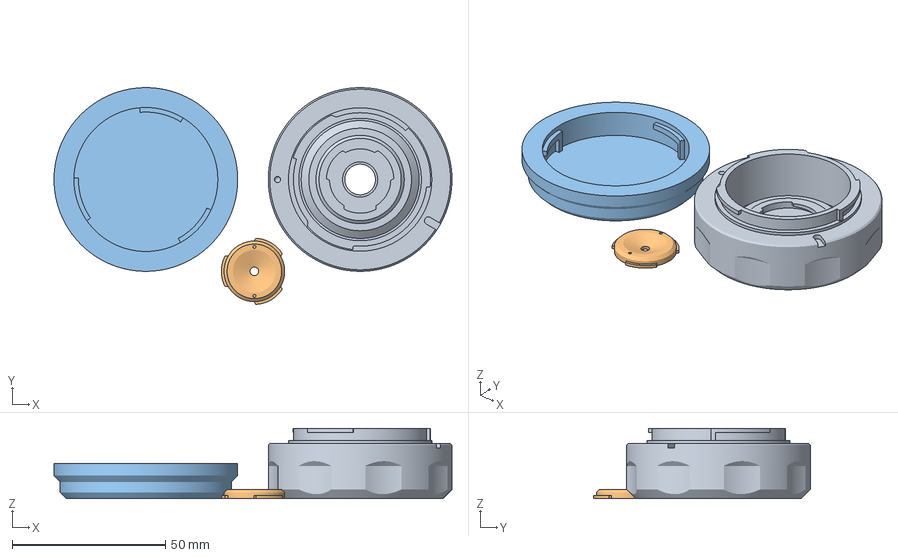
[picture p136: CAD file, 2023-11-17]
Sony E/STL/kodakFunsaver_sonyE_printOrientation.3mf
130.0 x 70.8 x 23.0 mm
kodakFunsaver_sonyE_body.stl
kodakFunsaver_lensLock.stl
baseRearCap_sonyE.stl
