Archive-663/kodakFunsaver/viewFinder/viewFinder_SQ/STL/kodakFunsaver_viewFinder_SQ_printOrientation.3mf

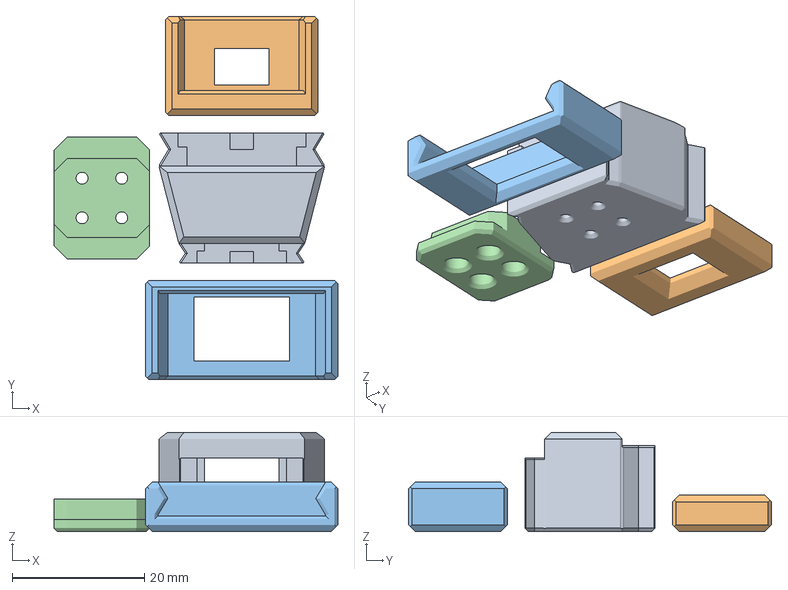
[picture p137: CAD file, 2023-11-20]
viewFinder/viewFinder_SQ/STL/kodakFunsaver_viewFinder_SQ_printOrientation.3mf
43.0 x 55.0 x 15.0 mm
kodakFunsaver_viewFinder_mainBody.stl
kodakFunsaver_viewFinder_rearCap.stl
kodakFunsaver_viewFinder_frontCap.stl
kodakFunsaver_viewFinder_coldShoe.stl
