Archive-663/kodakFunsaver/Canon FD/STL/baseRearCap_canonFD_KFS.stl

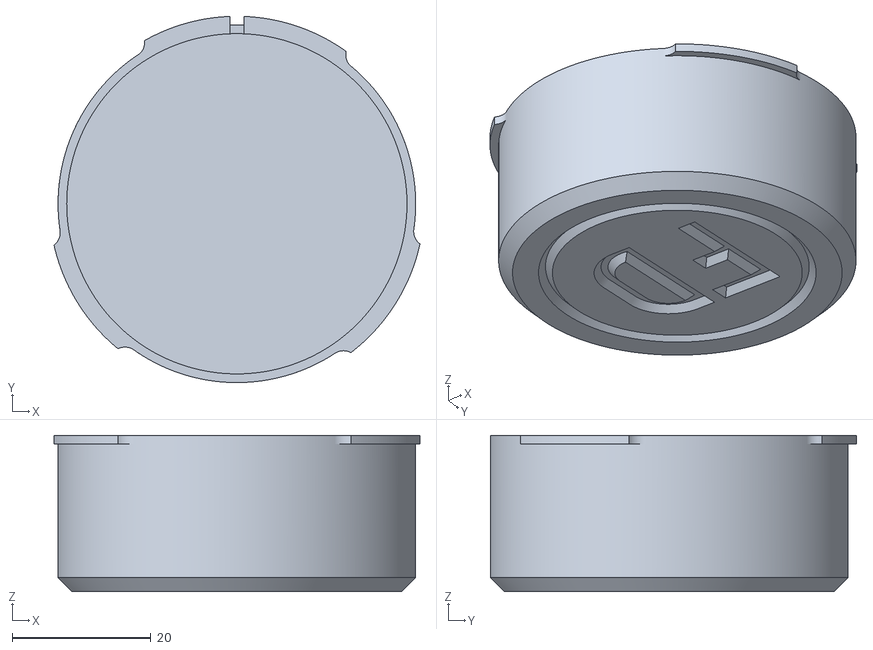
[picture p138: CAD file, 2023-11-17]
Canon FD/STL/baseRearCap_canonFD_KFS.stl
52.7 x 52.7 x 22.5
