Archive-663/kodakFunsaver/Fuji X/STL/kodakFunsaver_fujiX_body.stl

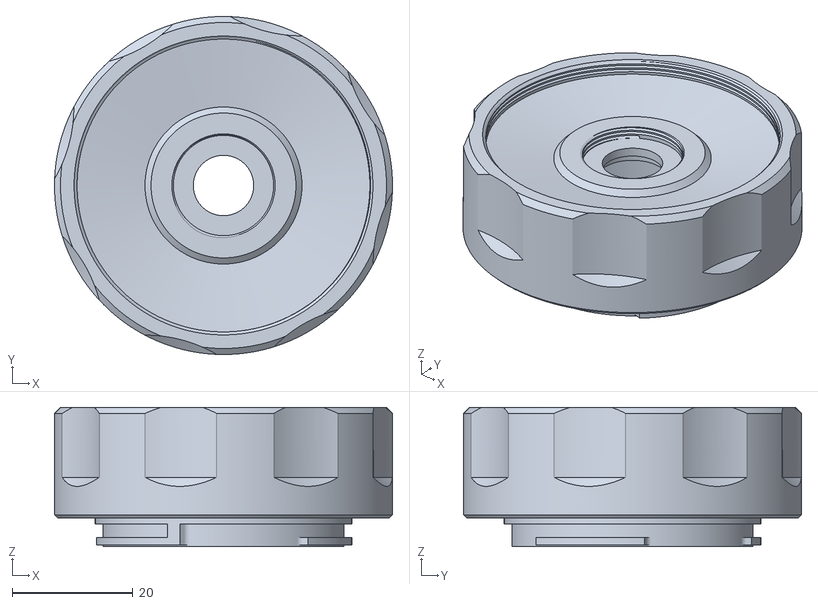
[picture p139: CAD file, 2023-11-17]
Fuji X/STL/kodakFunsaver_fujiX_body.stl
56.0 x 56.0 x 23.1
