Archive-663/kodakFunsaver/M42/STL/baseRearCap_M42_KFS.stl

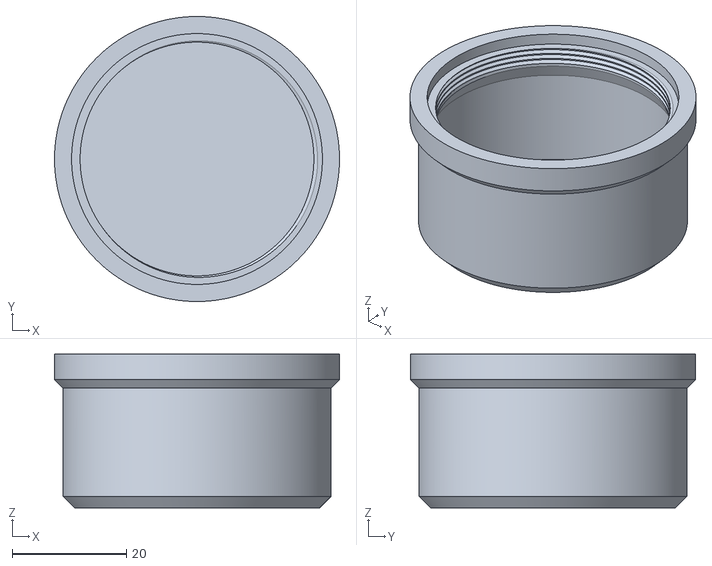
[picture p140: CAD file, 2023-11-17]
M42/STL/baseRearCap_M42_KFS.stl
50.0 x 50.0 x 27.0
