Archive-663/kodakFunsaver/MFT/STL/kodakFunsaver_MFT_body.stl

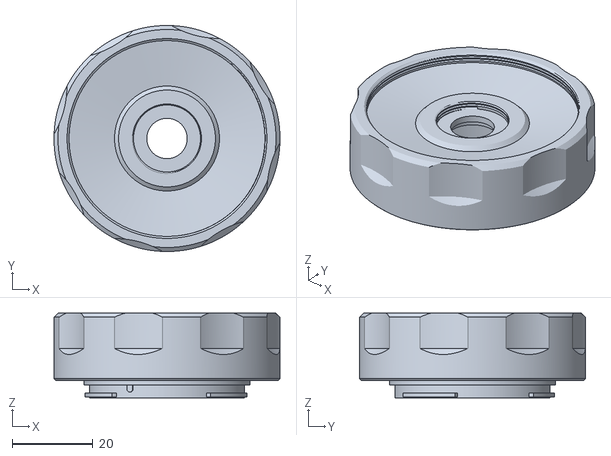
[picture p141: CAD file, 2023-11-17]
MFT/STL/kodakFunsaver_MFT_body.stl
56.0 x 56.0 x 21.0
