Archive-663/kodakFunsaver/Nikon F DX/STL/kodakFunsaver_nikonF_DX_printOrientation.3mf

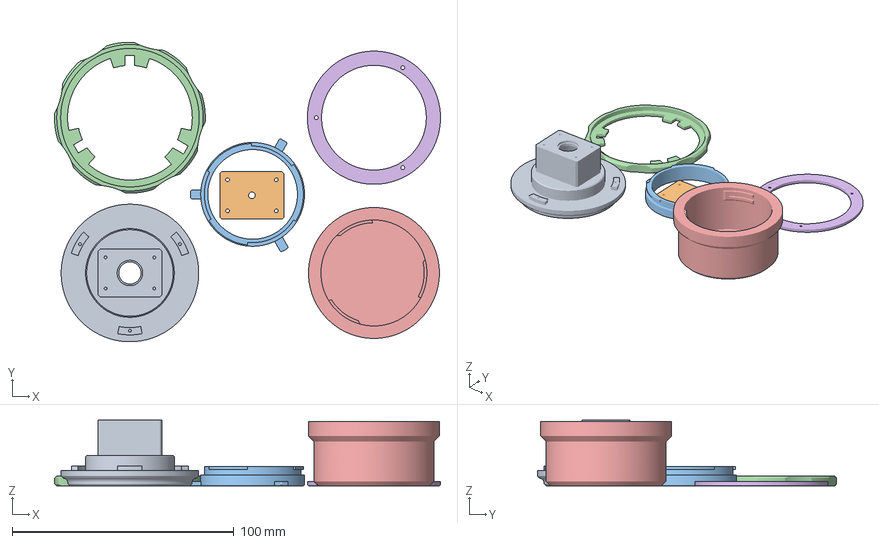
[picture p142: CAD file, 2023-11-17]
Nikon F DX/STL/kodakFunsaver_nikonF_DX_printOrientation.3mf
174.0 x 135.0 x 29.7 mm
kodakFunsaver_nikonF_DX_body.stl
kodakFunsaver_nikonF_DX_lensLock.stl
nishiKodak_nikonF-FX_mountFlange.stl
nishiKodak_nikonF-FX_mountLockRing.stl
baseRearCap_nikonF_KFS.stl
nishiKodak_nikonF-FX_mountCap.stl
