Archive-663/kodakFunsaver/Nikon F FX/STL/nishiKodak_nikonF-FX_mountFlange.stl

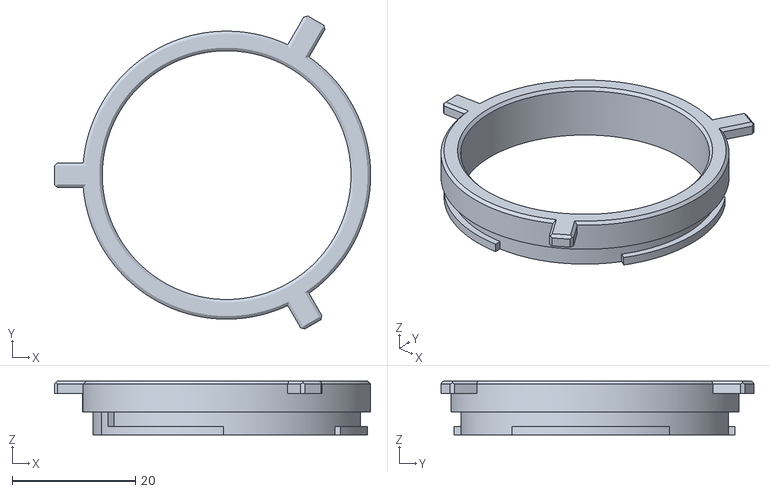
[picture p143: CAD file, 2023-11-17]
Nikon F FX/STL/nishiKodak_nikonF-FX_mountFlange.stl
51.4 x 50.9 x 8.75
