Archive-663/kodakFunsaver/Sony E/STL/kodakFunsaver_sonyE_body.stl

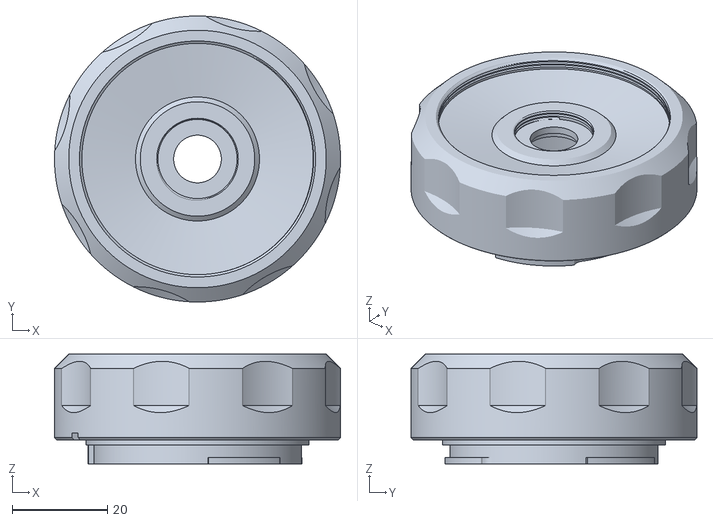
[picture p144: CAD file, 2023-11-17]
Sony E/STL/kodakFunsaver_sonyE_body.stl
60.0 x 60.0 x 23.0
