Archive-663/kodakFunsaver/Canon EF-S/STL/kodakFunsaver_canonEF-S_printOrientation.3mf

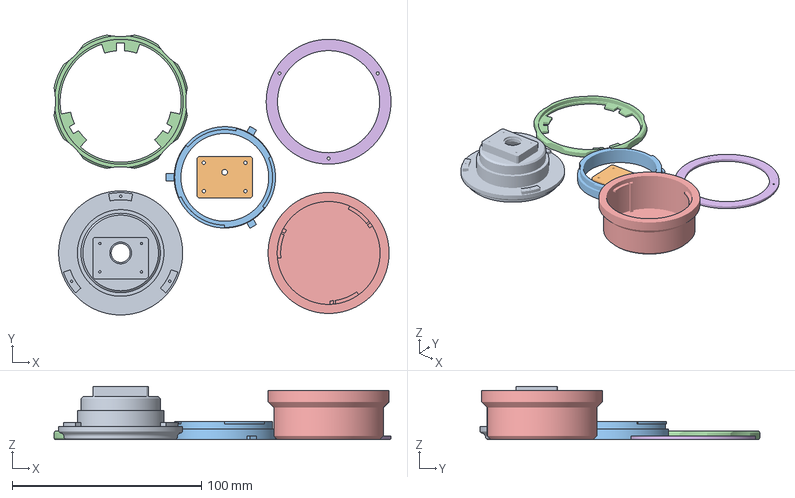
[picture p145: CAD file, 2023-11-17]
Canon EF-S/STL/kodakFunsaver_canonEF-S_printOrientation.3mf
178.3 x 148.1 x 28.2 mm
kodakFunsaver_canonEF-S_body.stl
kodakFunsaver_canonEF-S_lensLock.stl
nishiKodak_canonEF_mountFlange.stl
nishiKodak_canonEF_mountLockRing.stl
baseRearCap_canonEF_KFS.stl
nishiKodak_canonEF_mountCap.stl
