Archive-663/kodakFunsaver/M42/STL/nishiKodak_M42_mountThreads.stl

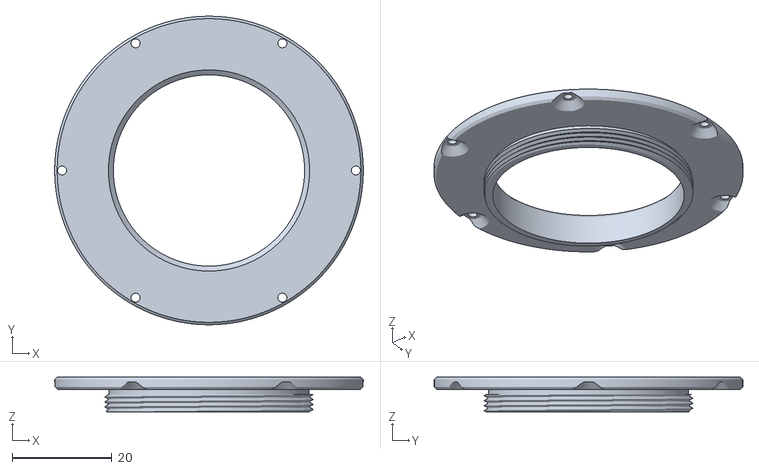
[picture p146: CAD file, 2023-11-17]
M42/STL/nishiKodak_M42_mountThreads.stl
62.1 x 62.0 x 7.00
