Archive-663/kodakFunsaver/Nikon F FX/STL/baseRearCap_nikonF_KFS.stl

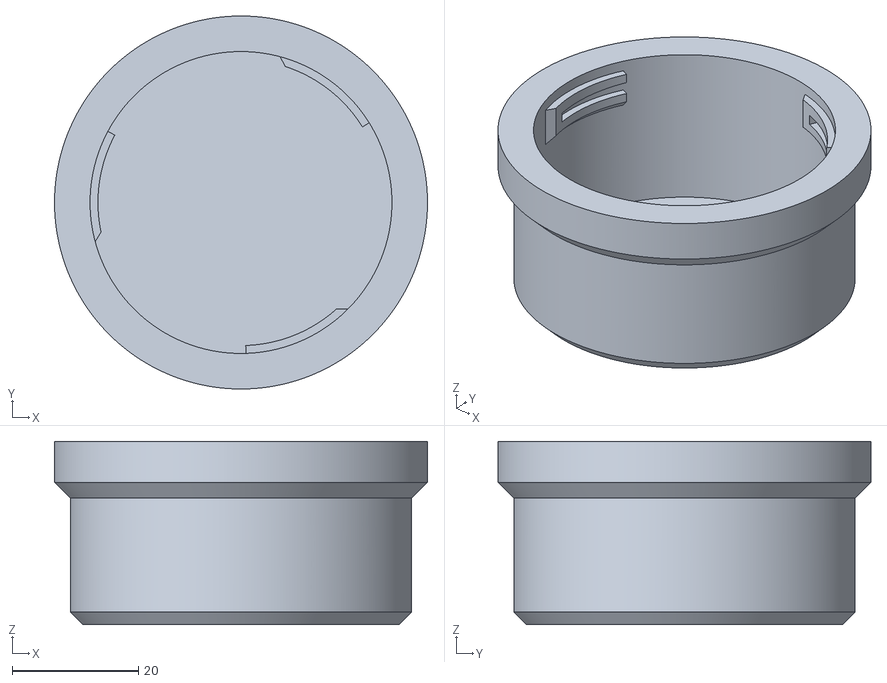
[picture p147: CAD file, 2023-11-17]
Nikon F FX/STL/baseRearCap_nikonF_KFS.stl
59.0 x 59.0 x 29.0
