Archive-663/kodakFunsaver/viewFinder/viewFinder_round/STL/kodakFunsaver_viewFinder_frontSight.stl

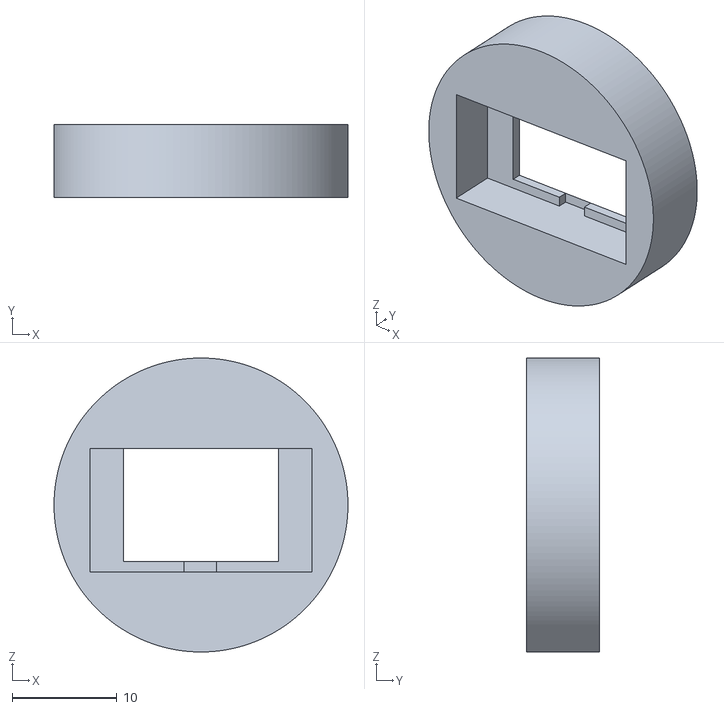
[picture p148: CAD file, 2023-06-24]
viewFinder/viewFinder_round/STL/kodakFunsaver_viewFinder_frontSight.stl
28.0 x 7.00 x 28.0
