Archive-663/kodakFunsaver/viewFinder/viewFinder_SQ/STL/kodakFunsaver_viewFinder_coldShoe.stl

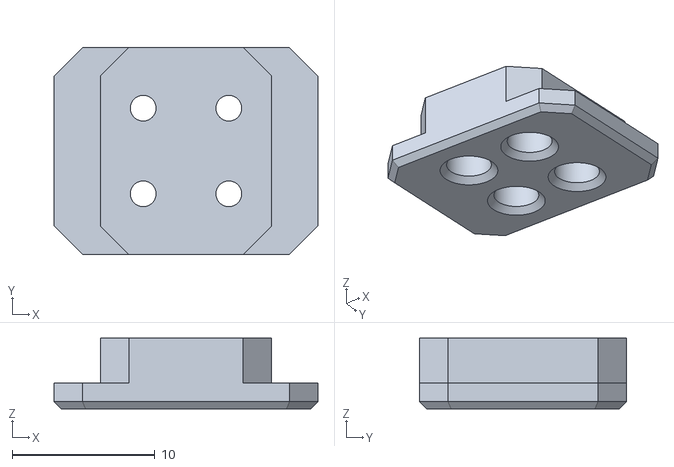
[picture p149: CAD file, 2023-11-20]
viewFinder/viewFinder_SQ/STL/kodakFunsaver_viewFinder_coldShoe.stl
18.5 x 14.5 x 4.95
