Archive-663/kodakFunsaver/Canon EF-S/STL/nishiKodak_canonEF_mountCap.stl

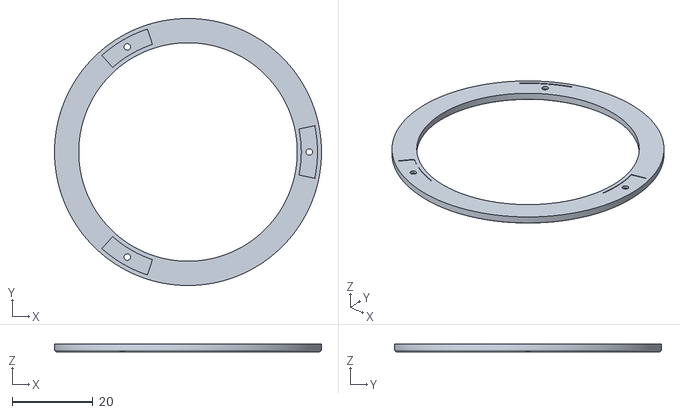
[picture p150: CAD file, 2023-11-17]
Canon EF-S/STL/nishiKodak_canonEF_mountCap.stl
66.0 x 66.0 x 2.00
