Archive-663/kodakFunsaver/M42/STL/kodakFunsaver_M42_body.stl

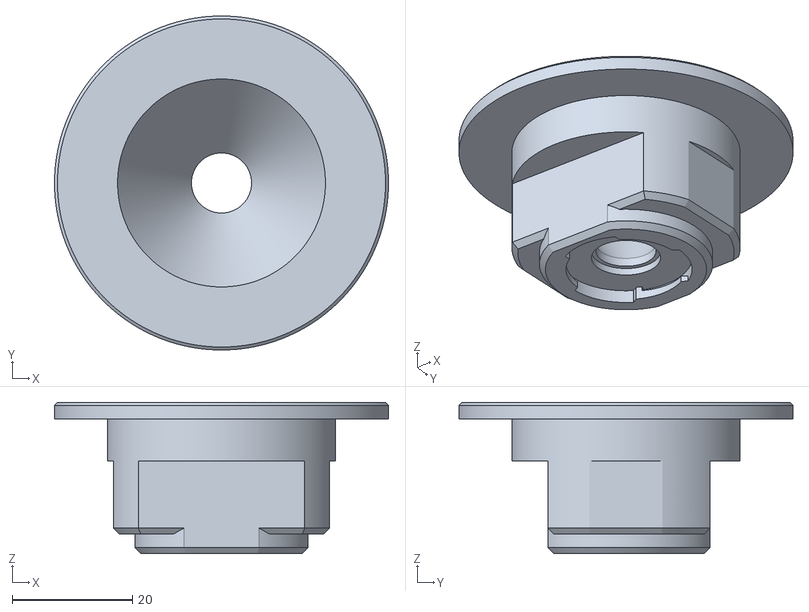
[picture p151: CAD file, 2023-11-17]
M42/STL/kodakFunsaver_M42_body.stl
55.6 x 55.6 x 25.2
