Archive-663/kodakFunsaver/Nikon F FX/STL/nishiKodak_nikonF-FX_mountLockRing.stl

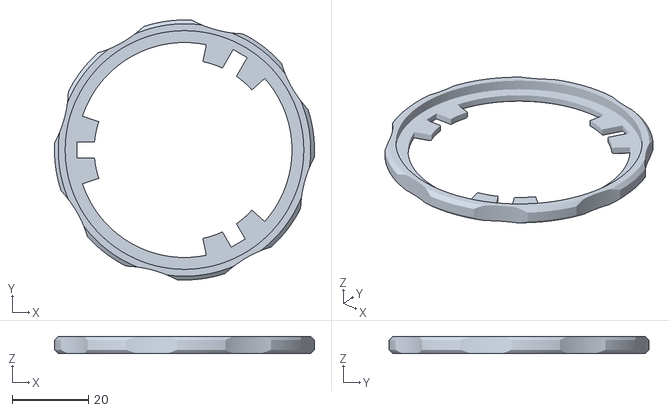
[picture p152: CAD file, 2023-11-17]
Nikon F FX/STL/nishiKodak_nikonF-FX_mountLockRing.stl
68.0 x 68.0 x 4.50
