Archive-663/kodakFunsaver/Nikon F FX/STL/kodakFunsaver_nikonF_FX_printOrientation.3mf

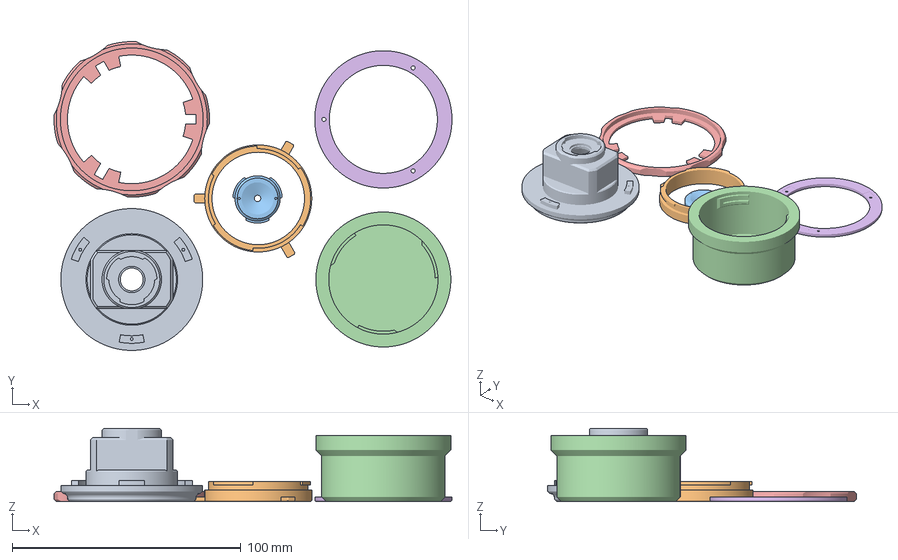
[picture p153: CAD file, 2023-11-17]
Nikon F FX/STL/kodakFunsaver_nikonF_FX_printOrientation.3mf
174.0 x 135.0 x 32.0 mm
kodakFunsaver_nikonF_FX_body.stl
nishiKodak_nikonF-FX_mountFlange.stl
kodakFunsaver_lensLock.stl
baseRearCap_nikonF_KFS.stl
nishiKodak_nikonF-FX_mountLockRing.stl
nishiKodak_nikonF-FX_mountCap.stl
